hotwolf/LoRaMeshNodes/SSNvD/stls/SSNvD_battery_frame_part1.stl

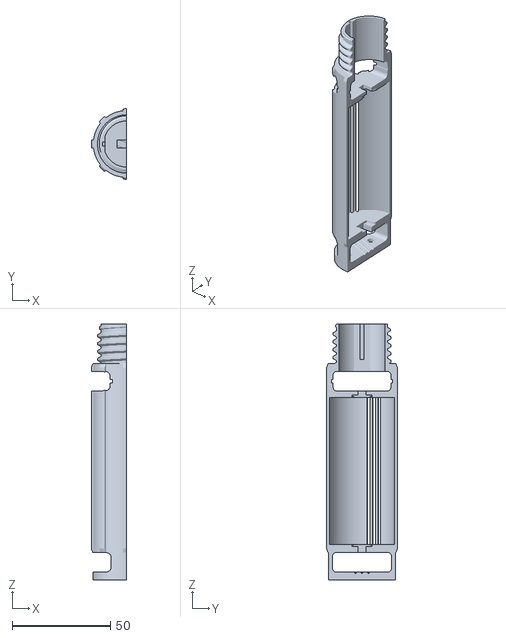
[picture p163: CAD file, 2026-01-20]
SSNvD/stls/SSNvD_battery_frame_part1.stl
18.0 x 36.0 x 130.0
