hotwolf/LoRaMeshNodes/MNvA/stls/MNvA_buttons.stl

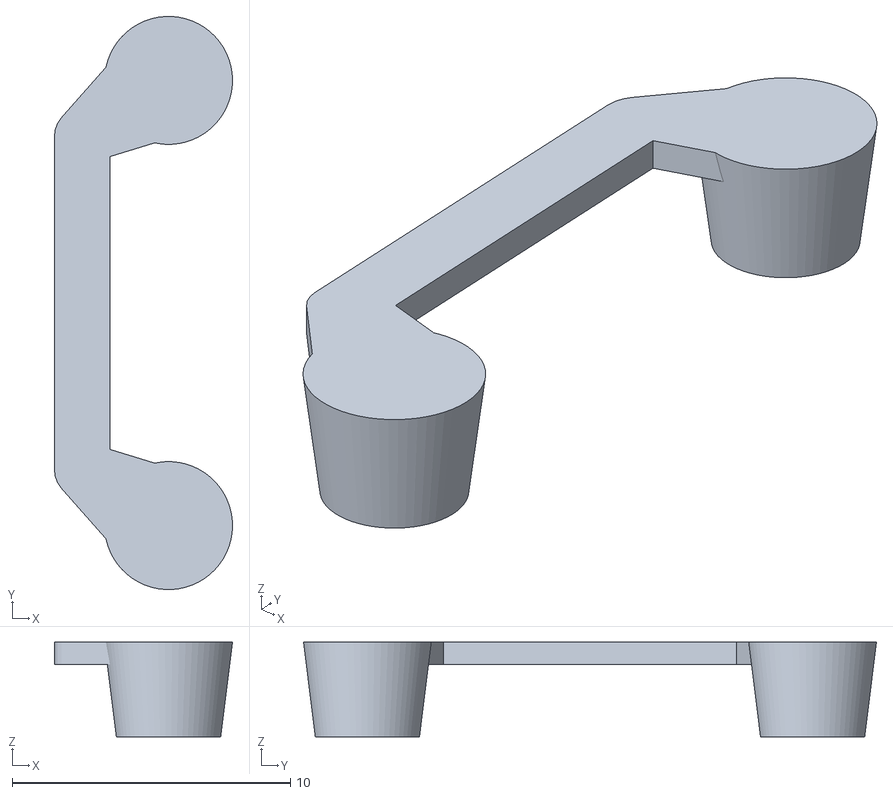
[picture p164: CAD file, 2026-01-26]
MNvA/stls/MNvA_buttons.stl
6.40 x 20.6 x 3.40
