hotwolf/LoRaMeshNodes/MSNvA/stls/MSNvA_stand.stl

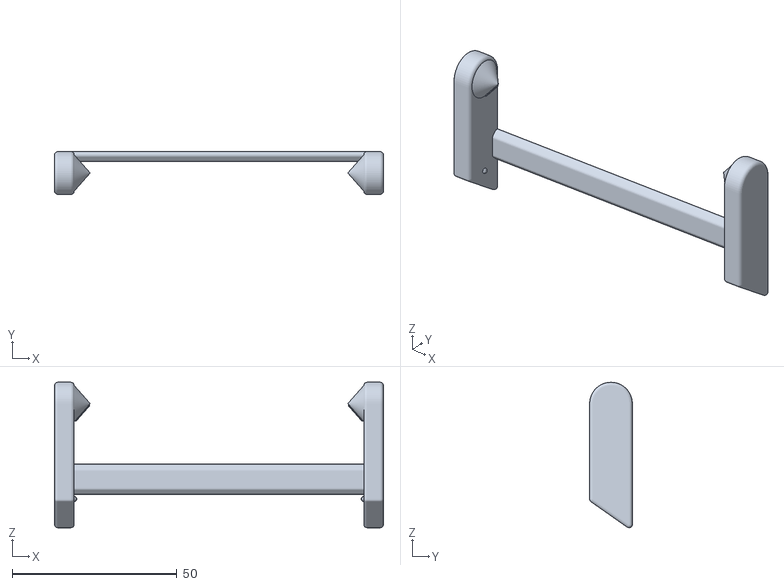
[picture p165: CAD file, 2025-09-03]
MSNvA/stls/MSNvA_stand.stl
100.0 x 13.0 x 44.2
