hotwolf/LoRaMeshNodes/MSNvB/stls/MSNvB_cov.stl

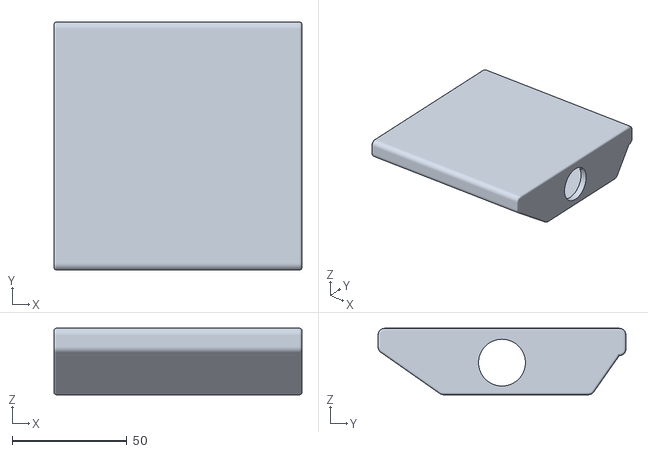
[picture p166: CAD file, 2025-09-03]
MSNvB/stls/MSNvB_cov.stl
108.0 x 108.0 x 29.0
