hotwolf/LoRaMeshNodes/SSNvA/stls/SSNvA_solar_mount.stl

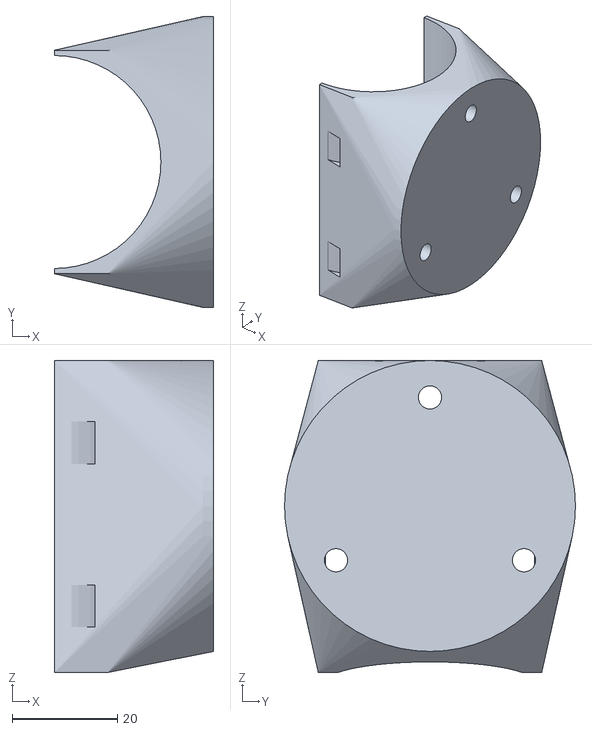
[picture p167: CAD file, 2026-01-20]
SSNvA/stls/SSNvA_solar_mount.stl
30.2 x 55.2 x 59.2
