hotwolf/LoRaMeshNodes/SSNvD/stls/SSNvD_solar_mount.stl

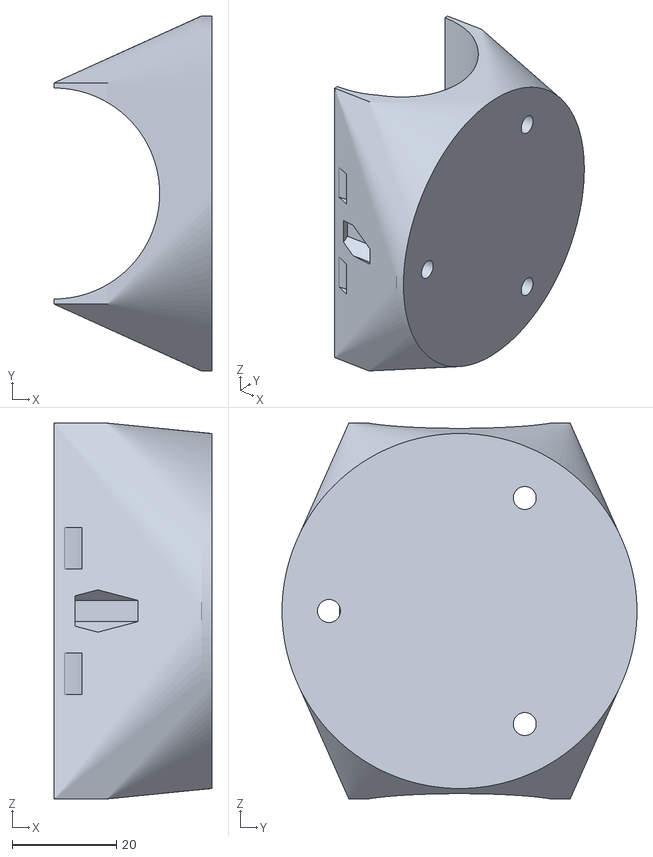
[picture p168: CAD file, 2026-01-20]
SSNvD/stls/SSNvD_solar_mount.stl
30.2 x 68.0 x 72.0
