hotwolf/LoRaMeshNodes/MSNvA/stls/MSNvA_cov.stl

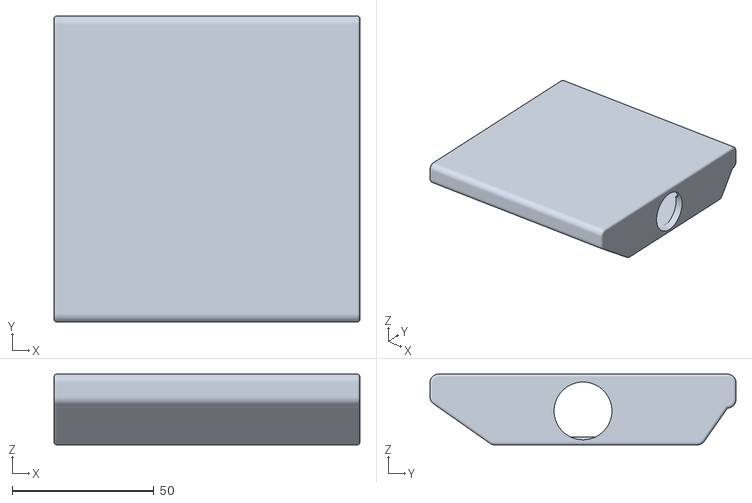
[picture p169: CAD file, 2025-08-17]
MSNvA/stls/MSNvA_cov.stl
108.0 x 108.0 x 25.0
