hotwolf/LoRaMeshNodes/MSNvB/stls/MSNvB_stand.stl

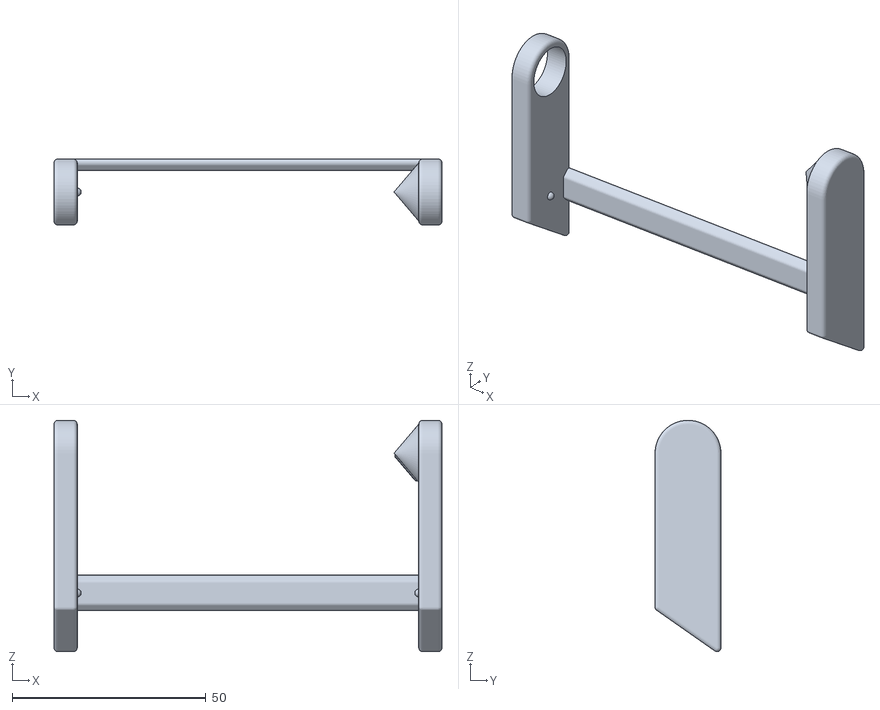
[picture p170: CAD file, 2025-09-03]
MSNvB/stls/MSNvB_stand.stl
100.0 x 17.0 x 59.6
