hotwolf/LoRaMeshNodes/SSNvA/stls/SSNvA_battery_cable_clamp.stl

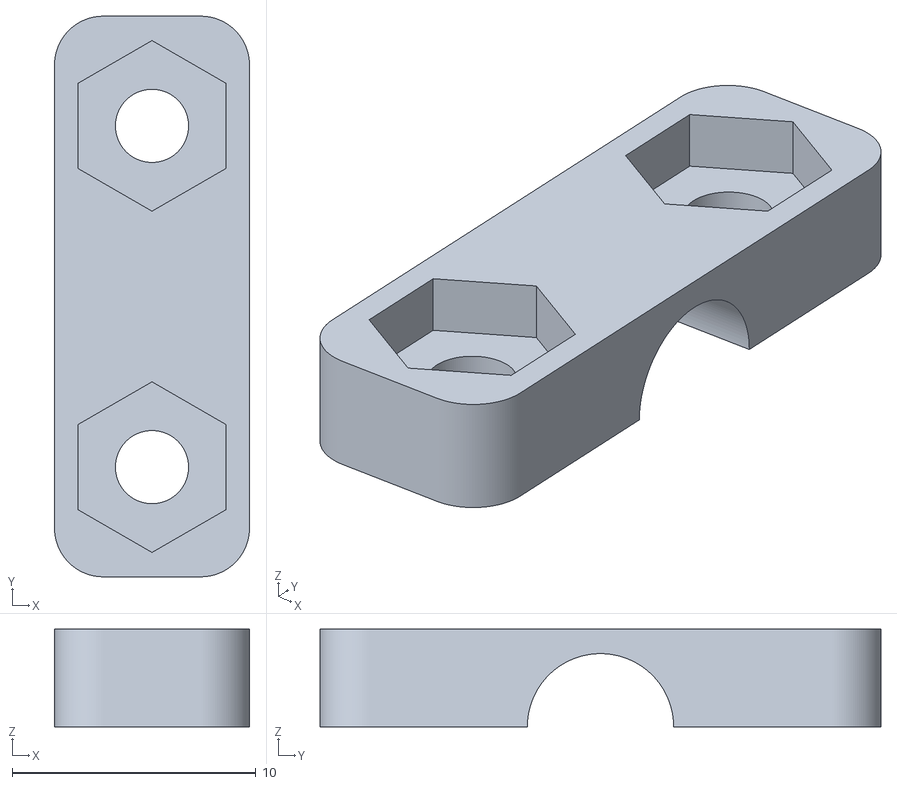
[picture p171: CAD file, 2025-10-28]
SSNvA/stls/SSNvA_battery_cable_clamp.stl
8.00 x 23.0 x 4.00
