hotwolf/LoRaMeshNodes/SSNvB/stls/SSNvB_LOEncMount.stl

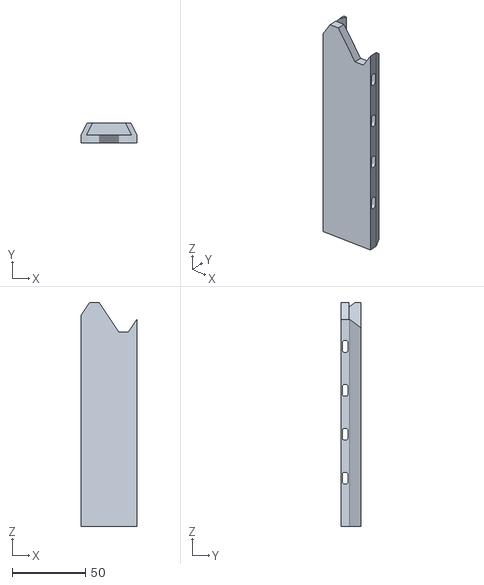
[picture p172: CAD file, 2026-02-28]
SSNvB/stls/SSNvB_LOEncMount.stl
38.0 x 14.0 x 153.0
