hotwolf/LoRaMeshNodes/SSNvD/stls/SSNvD_antenna_top.stl

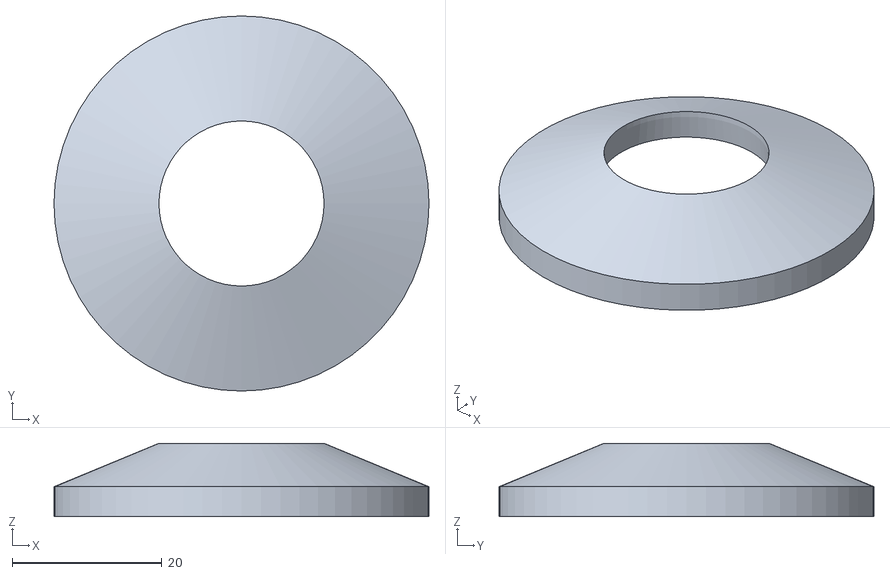
[picture p173: CAD file, 2026-01-19]
SSNvD/stls/SSNvD_antenna_top.stl
50.0 x 50.0 x 9.79
