hotwolf/LoRaMeshNodes/MSNvA/stls/MSNvA_buttons.stl

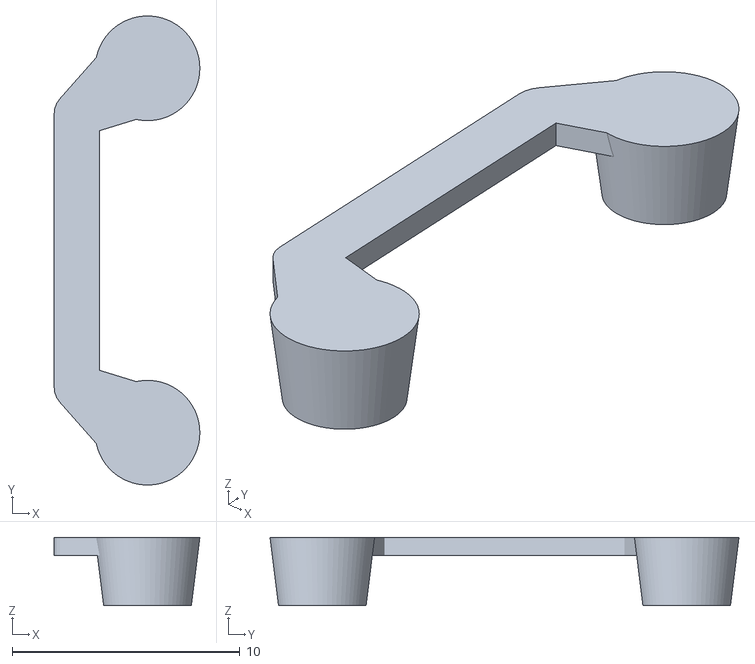
[picture p174: CAD file, 2025-08-17]
MSNvA/stls/MSNvA_buttons.stl
6.40 x 20.6 x 3.00
