hotwolf/LoRaMeshNodes/SSNvB/stls/SSNvB_lEndcap.stl

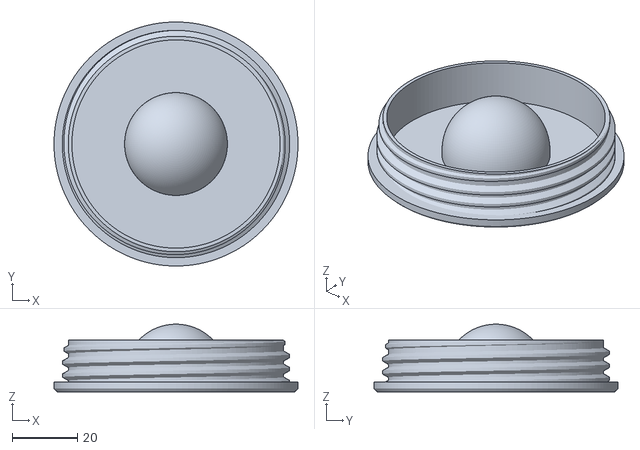
[picture p175: CAD file, 2026-02-17]
SSNvB/stls/SSNvB_lEndcap.stl
75.0 x 75.0 x 20.8
