hotwolf/LoRaMeshNodes/SSNvD/stls/SSNvD_end_cap_ring.stl

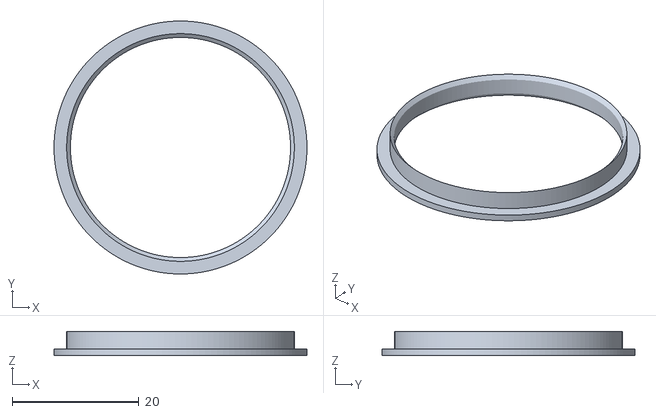
[picture p176: CAD file, 2026-01-19]
SSNvD/stls/SSNvD_end_cap_ring.stl
40.0 x 40.0 x 3.80
