hotwolf/LoRaMeshNodes/SSNvA/stls/SSNvA_antenna_part2.stl

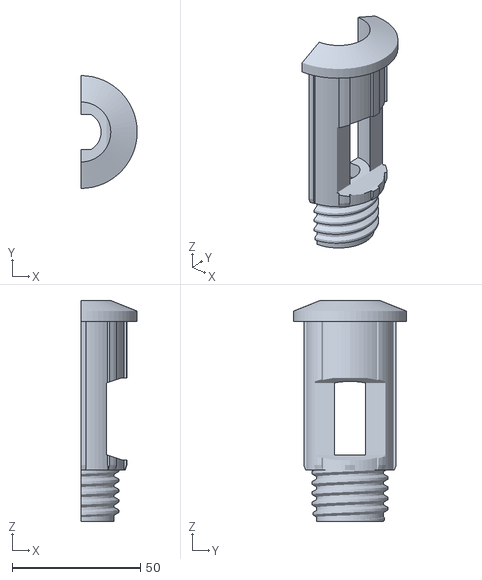
[picture p177: CAD file, 2025-10-27]
SSNvA/stls/SSNvA_antenna_part2.stl
22.0 x 44.0 x 86.1
