hotwolf/LoRaMeshNodes/SSNvB/stls/SSNvB_antennaMountFastener.stl

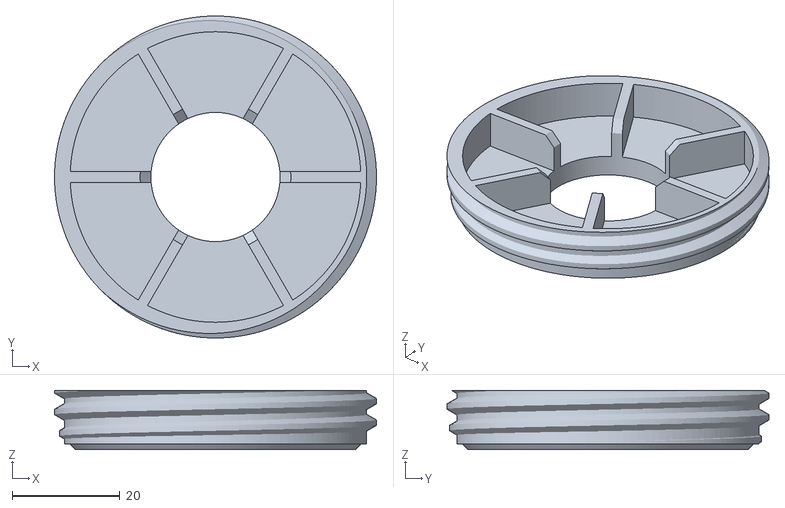
[picture p178: CAD file, 2026-02-17]
SSNvB/stls/SSNvB_antennaMountFastener.stl
59.8 x 59.8 x 11.0
