hotwolf/LoRaMeshNodes/SSNvD/stls/SSNvD_battery_cable_clamp.stl

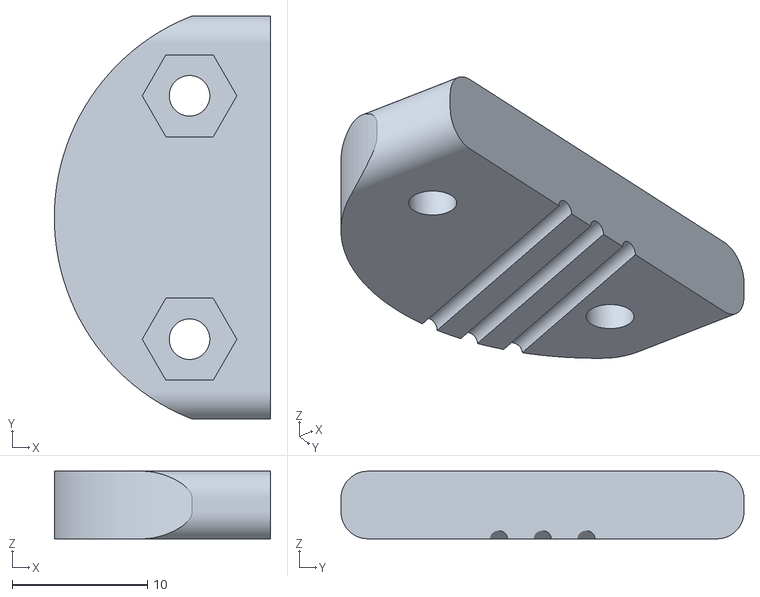
[picture p179: CAD file, 2026-01-19]
SSNvD/stls/SSNvD_battery_cable_clamp.stl
16.0 x 29.8 x 5.00
