hotwolf/LoRaMeshNodes/SSNvB/stls/SSNvB_uEndcap.stl

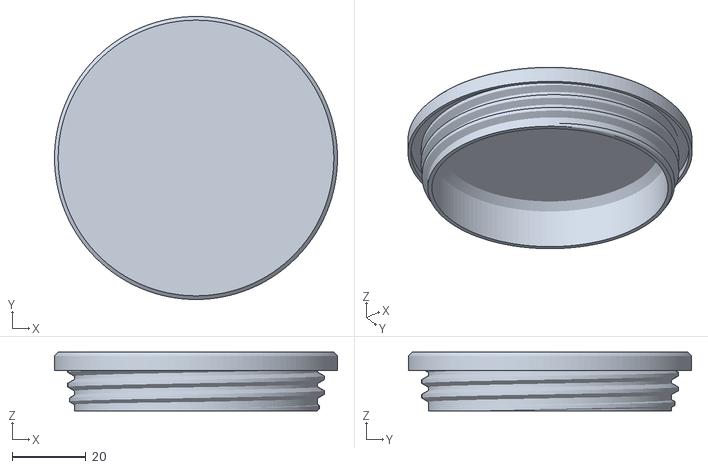
[picture p180: CAD file, 2026-02-17]
SSNvB/stls/SSNvB_uEndcap.stl
77.0 x 77.0 x 16.0
