hotwolf/LoRaMeshNodes/SSNvD/stls/SSNvD_radio_frame_part2.stl

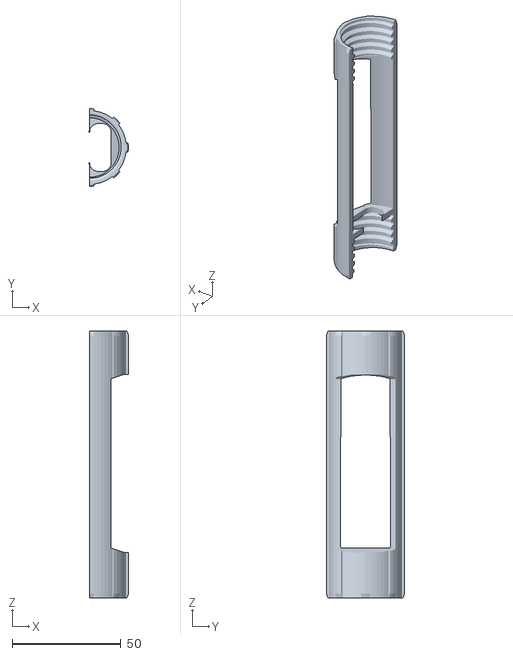
[picture p181: CAD file, 2026-01-19]
SSNvD/stls/SSNvD_radio_frame_part2.stl
18.0 x 36.0 x 123.0
