hotwolf/LoRaMeshNodes/SSNvB/stls/SSNvB_battery_frame_part1.stl

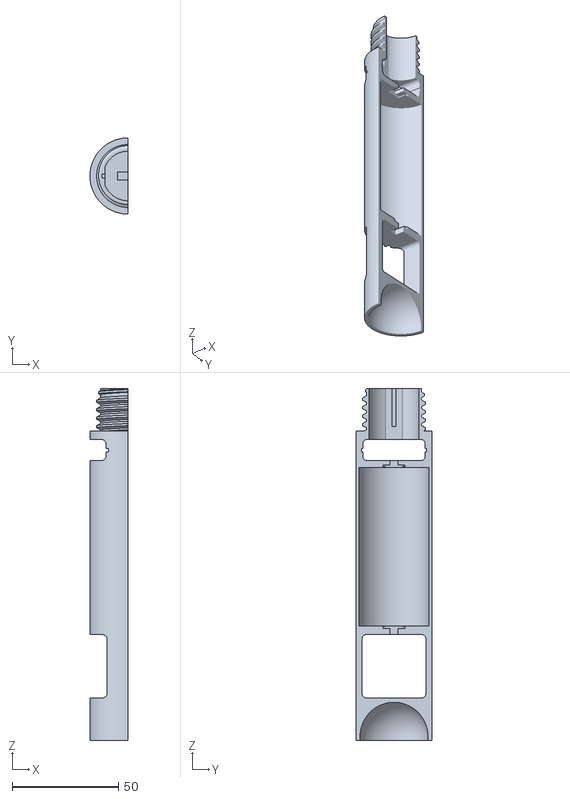
[picture p183: CAD file, 2026-02-15]
SSNvB/stls/SSNvB_battery_frame_part1.stl
18.0 x 36.0 x 166.0
