hotwolf/LoRaMeshNodes/SSNvD/stls/SSNvD_spacer.stl

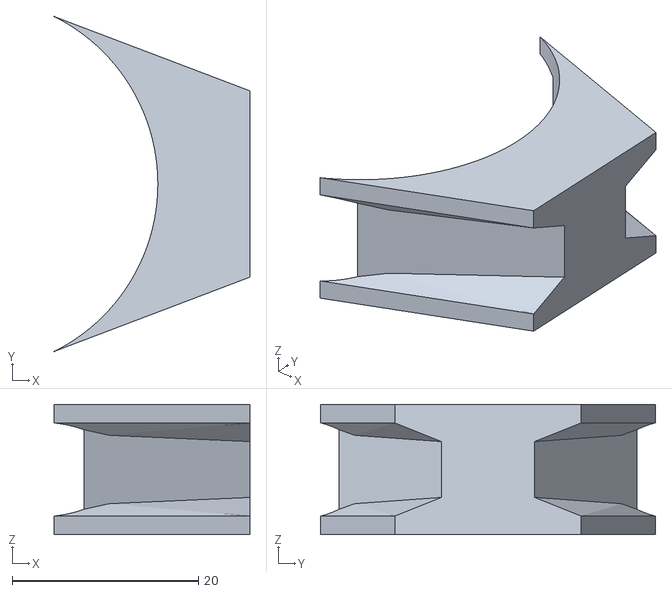
[picture p184: CAD file, 2026-01-19]
SSNvD/stls/SSNvD_spacer.stl
21.1 x 36.0 x 14.0
