hotwolf/LoRaMeshNodes/SSNvA/stls/SSNvA_battery_frame_part2.stl

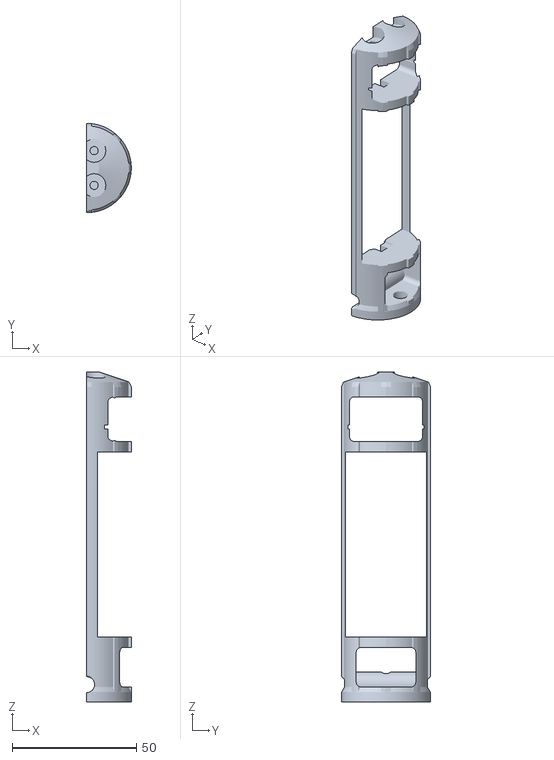
[picture p185: CAD file, 2025-10-27]
SSNvA/stls/SSNvA_battery_frame_part2.stl
18.0 x 36.0 x 133.0
