hotwolf/LoRaMeshNodes/SSNvB/stls/SSNvB_battery_frame_part2.stl

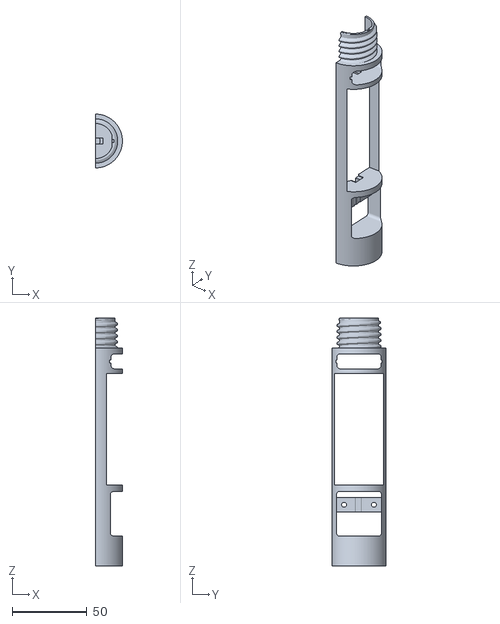
[picture p186: CAD file, 2026-02-15]
SSNvB/stls/SSNvB_battery_frame_part2.stl
18.0 x 36.0 x 166.0
