hotwolf/LoRaMeshNodes/SSNvD/stls/SSNvD_end_cap.stl

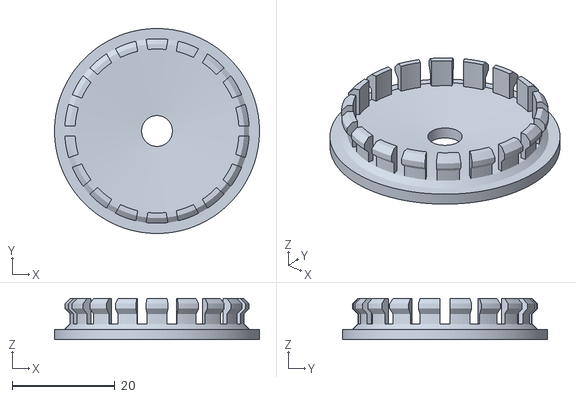
[picture p187: CAD file, 2026-01-19]
SSNvD/stls/SSNvD_end_cap.stl
40.0 x 40.0 x 8.00
