hotwolf/LoRaMeshNodes/SSNvA/stls/SSNvA_antenna_top.stl

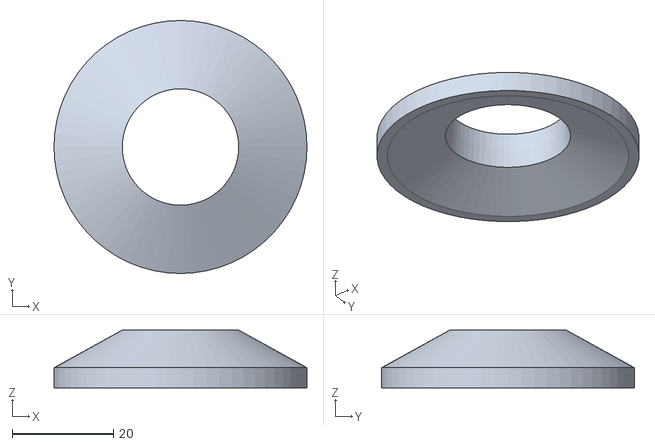
[picture p188: CAD file, 2025-10-20]
SSNvA/stls/SSNvA_antenna_top.stl
50.0 x 50.0 x 11.4
