hotwolf/LoRaMeshNodes/SSNvB/stls/SSNvB_EndcapThread.stl

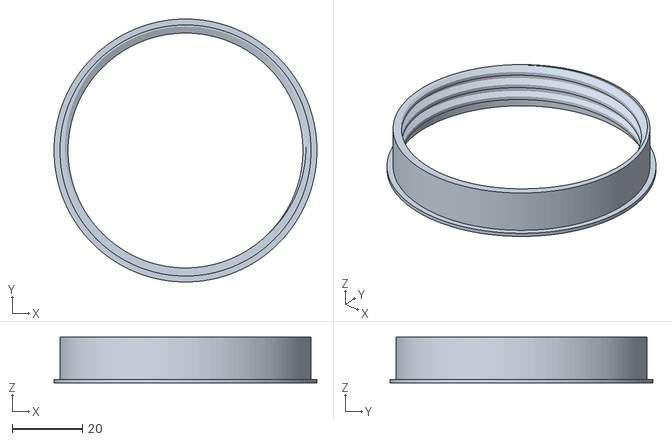
[picture p189: CAD file, 2026-02-15]
SSNvB/stls/SSNvB_EndcapThread.stl
75.0 x 75.0 x 13.0
