hotwolf/LoRaMeshNodes/SSNvD/stls/SSNvD_radio_frame_part1.stl

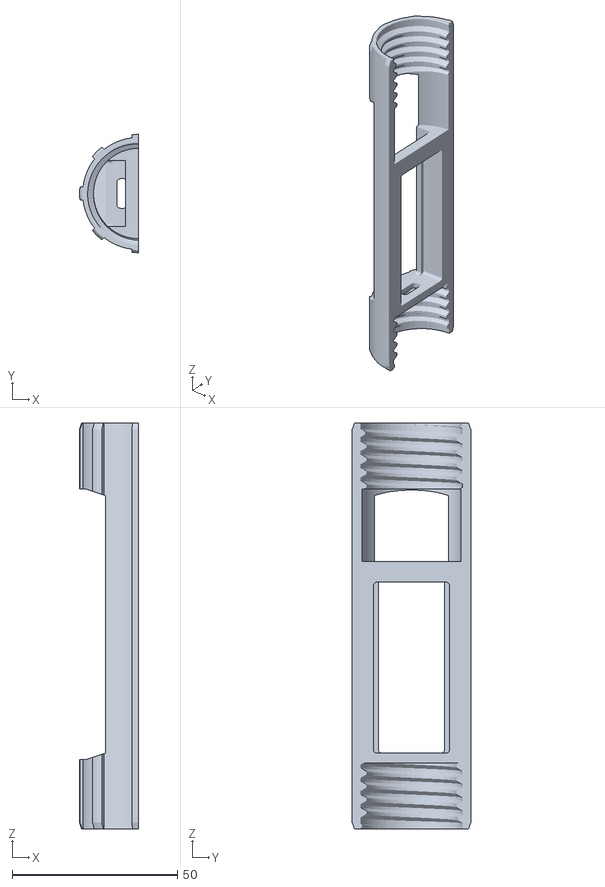
[picture p190: CAD file, 2026-01-19]
SSNvD/stls/SSNvD_radio_frame_part1.stl
18.0 x 36.0 x 123.0
