hotwolf/LoRaMeshNodes/SSNvA/stls/SSNvA_scrutonM40.stl

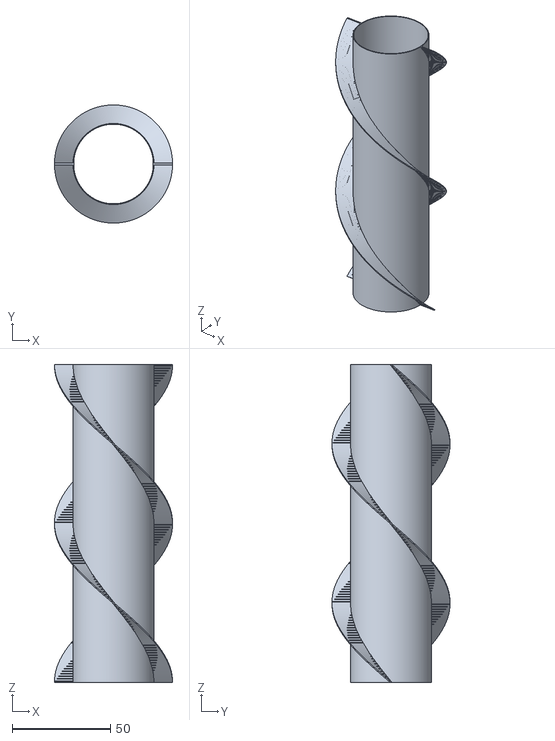
[picture p191: CAD file, 2025-10-20]
SSNvA/stls/SSNvA_scrutonM40.stl
60.0 x 60.0 x 161.6
