hotwolf/LoRaMeshNodes/SSNvB/stls/SSNvB_antenna.stl

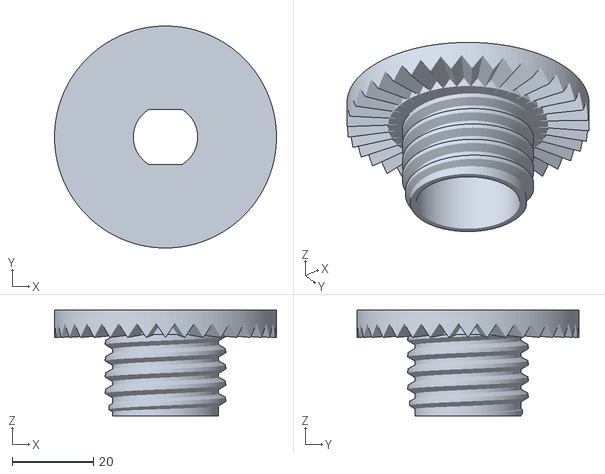
[picture p192: CAD file, 2026-02-15]
SSNvB/stls/SSNvB_antenna.stl
54.6 x 54.6 x 26.0
