hotwolf/LoRaMeshNodes/SSNvD/stls/SSNvD_antenna_part1.stl

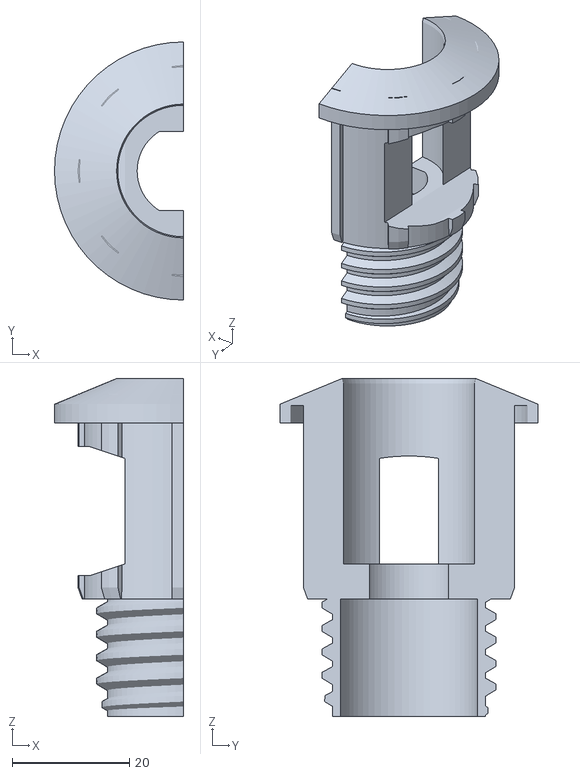
[picture p193: CAD file, 2026-01-19]
SSNvD/stls/SSNvD_antenna_part1.stl
22.0 x 44.0 x 57.6
