hotwolf/LoRaMeshNodes/SSNvA/stls/SSNvA_cable_clamp.stl

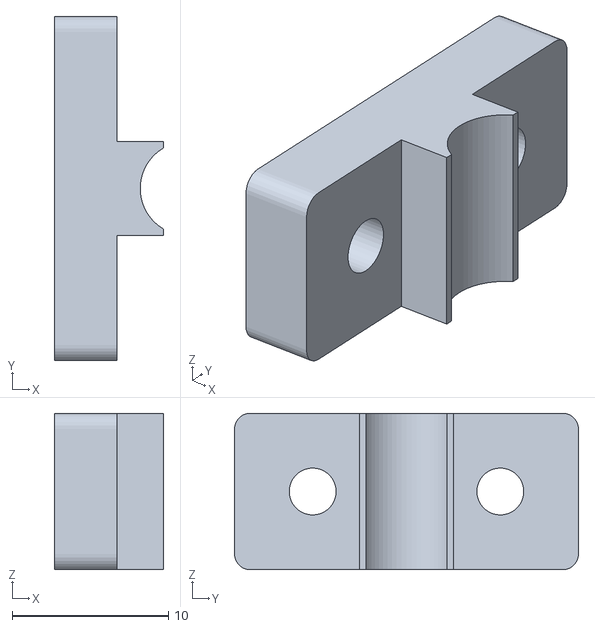
[picture p194: CAD file, 2025-10-20]
SSNvA/stls/SSNvA_cable_clamp.stl
7.00 x 22.0 x 10.0
