hotwolf/LoRaMeshNodes/SSNvB/stls/SSNvB_antennaMountThread.stl

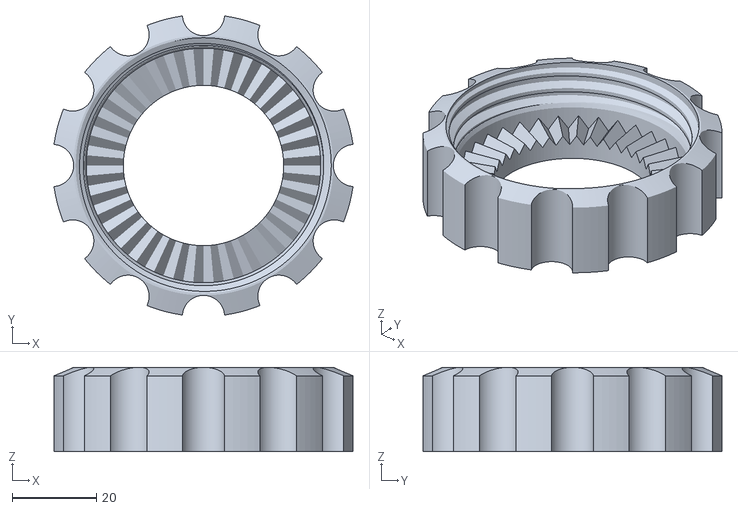
[picture p195: CAD file, 2026-02-15]
SSNvB/stls/SSNvB_antennaMountThread.stl
70.9 x 70.9 x 20.0
