hotwolf/LoRaMeshNodes/SSNvB/stls/SSNvB_battery_cable_clamp.stl

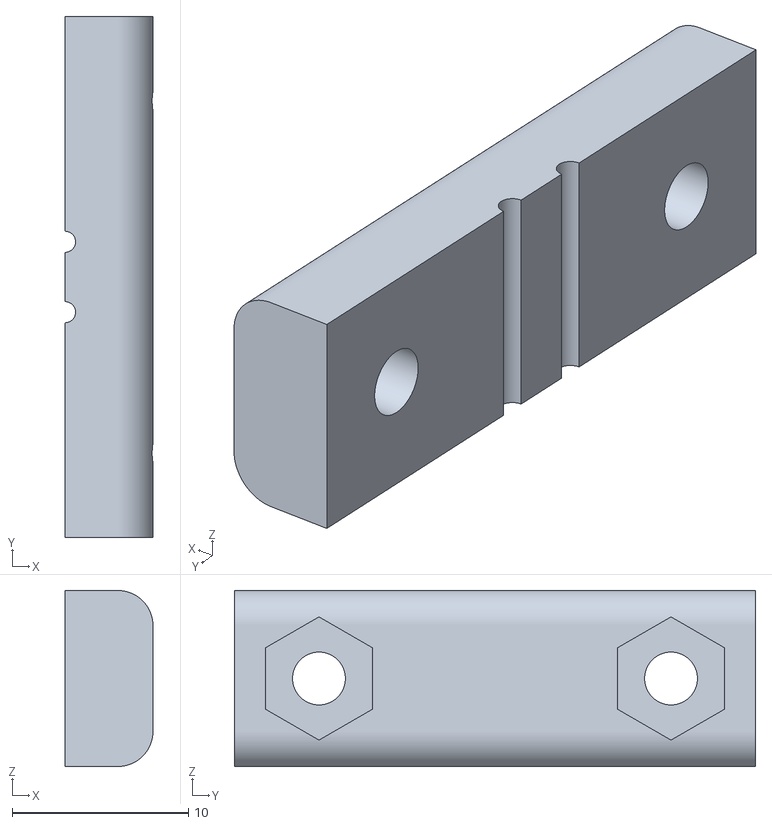
[picture p196: CAD file, 2026-02-15]
SSNvB/stls/SSNvB_battery_cable_clamp.stl
5.00 x 29.6 x 10.0
