hotwolf/LoRaMeshNodes/SSNvA/bom/SSNvA_pole_assembly.txt

SSNvA_pole_assembly:
Vitamins:
  1 Conduit diameter 40mmlength 2000mm

Printed:
  2 SSNvA_scrutonM40.stl
