hotwolf/LoRaMeshNodes/SSNvA/bom/SSNvA_radio_frame_assembly.txt

SSNvA_radio_frame_assembly:
Printed:
  1 SSNvA_radio_frame_part1.stl
  1 SSNvA_radio_frame_part2.stl
