hotwolf/LoRaMeshNodes/SSNvA/bom/SSNvA_top_assembly.txt

SSNvA_top_assembly:

Assemblies:
  1 SSNvA_antenna_assembly
  1 SSNvA_radio_assembly
