hotwolf/LoRaMeshNodes/MSNvB/bom/MSNvB_assembly.txt

MSNvB_assembly:
Printed:
  1 MSNvB_cov.stl

Assemblies:
  1 MSNvB_enc_assembly
