hotwolf/LoRaMeshNodes/MSNvA/bom/MSNvA_enc_assembly.txt

MSNvA_enc_assembly:
Vitamins:
  1 Solar Panel 100x100mm² 5V 3W

Printed:
  1 MSNvA_top.stl

Assemblies:
  1 MSNvA_lEnc_assembly
