hotwolf/LoRaMeshNodes/MSNvA/bom/MSNvA_assembly.txt

MSNvA_assembly:
Printed:
  1 MSNvA_cov.stl

Assemblies:
  1 MSNvA_enc_assembly
