hotwolf/LoRaMeshNodes/MSNvA/bom/MSNvA_lEnc_assembly.txt

MSNvA_lEnc_assembly:
Vitamins:
  1 Lithium-Polymer-Akku 3,7V 2500mAh
  1 Solar Panel 100x100mm² 5V 3W
  1 Antenna 20cm LoRa Antenna
  1 Nut M6.25 x 1.8mm 
  1 Heltec T144
  1 Heltec L76K_GNSS Module
  1 Washer star M6.4 x 0.6mm

Printed:
  1 MSNvA_buttons.stl
  1 MSNvA_lEnc.stl
  1 MSNvA_stand.stl
