hotwolf/LoRaMeshNodes/LiFePo4Charger/assemblies/LiFePo4Charger_assembly.png

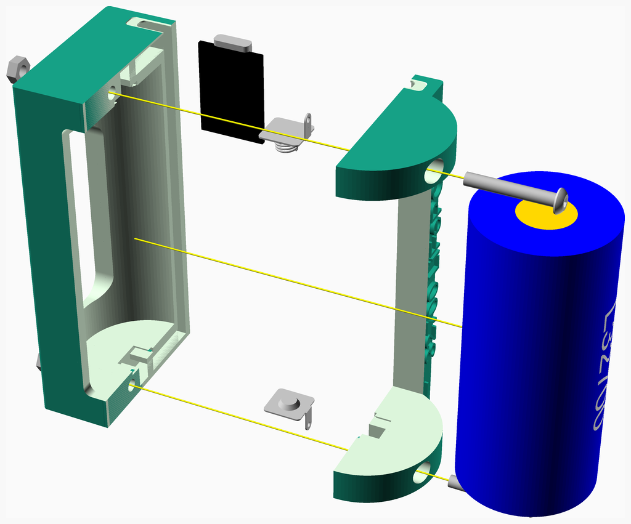
LiFePo4Charger/assemblies/LiFePo4Charger_assembly.png
