hotwolf/LoRaMeshNodes/MNvA/assemblies/MNvA_assembled_tn.png

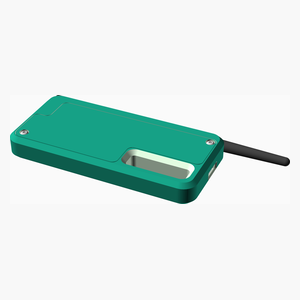
MNvA/assemblies/MNvA_assembled_tn.png
