hotwolf/LoRaMeshNodes/MNvA/assemblies/MNvA_assembly_tn.png

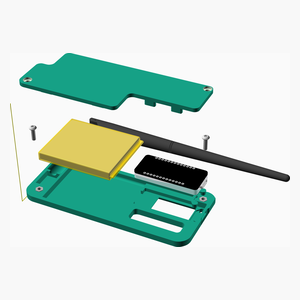
MNvA/assemblies/MNvA_assembly_tn.png
