hotwolf/LoRaMeshNodes/MNvA/assemblies/MNvA_lEnc_assembly_tn.png

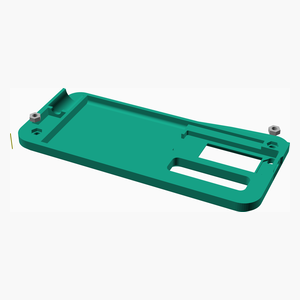
MNvA/assemblies/MNvA_lEnc_assembly_tn.png
