hotwolf/LoRaMeshNodes/MNvB/assemblies/MNvB_assembly.png

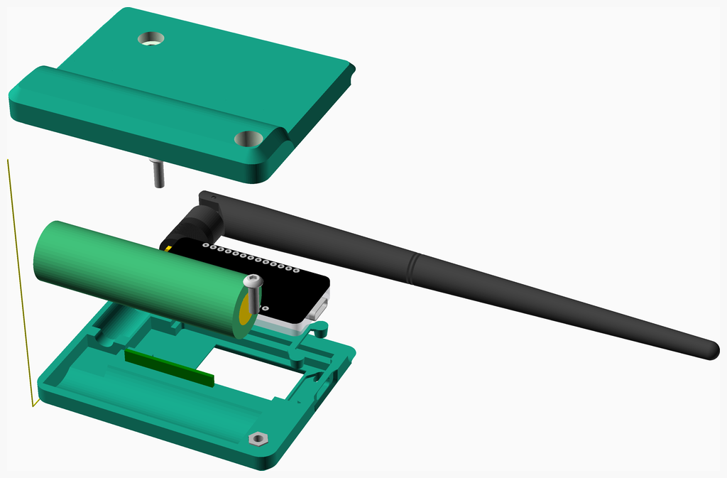
MNvB/assemblies/MNvB_assembly.png
