hotwolf/LoRaMeshNodes/MNvB/assemblies/MNvB_lEnc_assembled.png

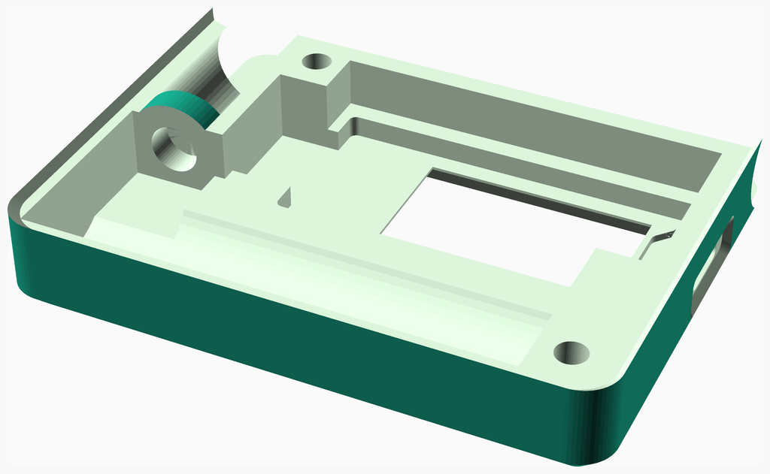
MNvB/assemblies/MNvB_lEnc_assembled.png
