hotwolf/LoRaMeshNodes/MNvB/assemblies/MNvB_lEnc_assembly.png

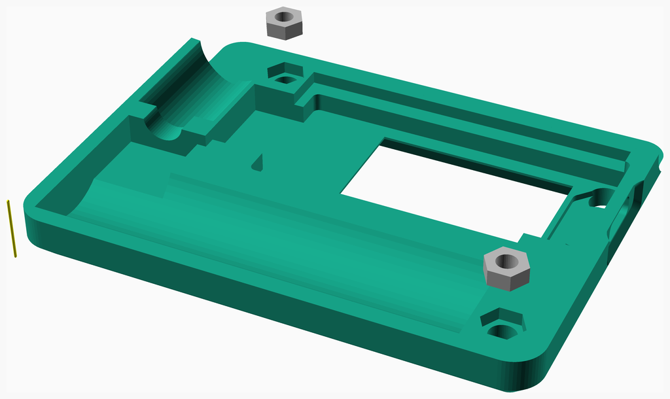
MNvB/assemblies/MNvB_lEnc_assembly.png
