hotwolf/LoRaMeshNodes/MSNvA/assemblies/MSNvA_assembled_tn.png

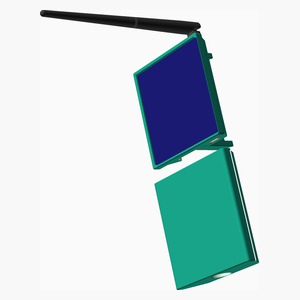
MSNvA/assemblies/MSNvA_assembled_tn.png
