hotwolf/LoRaMeshNodes/MSNvA/assemblies/MSNvA_assembly_tn.png

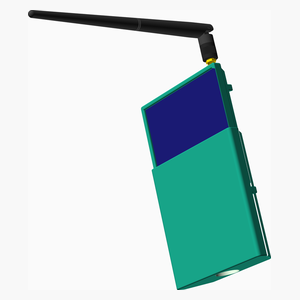
MSNvA/assemblies/MSNvA_assembly_tn.png
