hotwolf/LoRaMeshNodes/MSNvA/assemblies/MSNvA_enc_assembly_tn.png

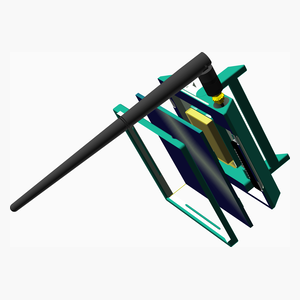
MSNvA/assemblies/MSNvA_enc_assembly_tn.png
