hotwolf/LoRaMeshNodes/MSNvA/assemblies/MSNvA_lEnc_assembly_tn.png

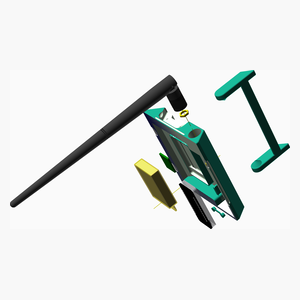
MSNvA/assemblies/MSNvA_lEnc_assembly_tn.png
