hotwolf/LoRaMeshNodes/MSNvB/assemblies/MSNvB_assembly_tn.png

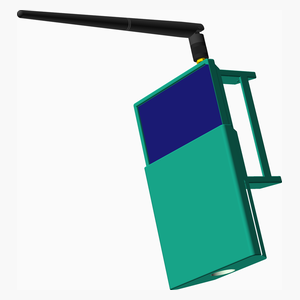
MSNvB/assemblies/MSNvB_assembly_tn.png
