hotwolf/LoRaMeshNodes/MSNvB/assemblies/MSNvB_enc_assembly_tn.png

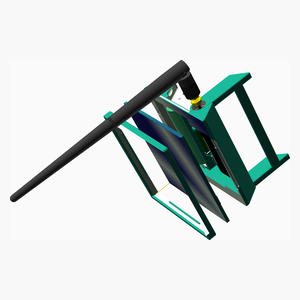
MSNvB/assemblies/MSNvB_enc_assembly_tn.png
