hotwolf/LoRaMeshNodes/MSNvB/assemblies/MSNvB_lEnc_assembly_tn.png

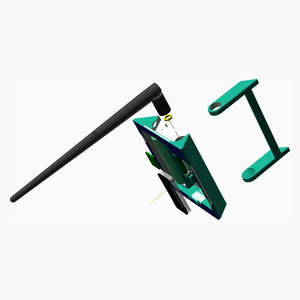
MSNvB/assemblies/MSNvB_lEnc_assembly_tn.png
