hotwolf/LoRaMeshNodes/SSNvA/assemblies/SSNvA_antenna_assembly.png

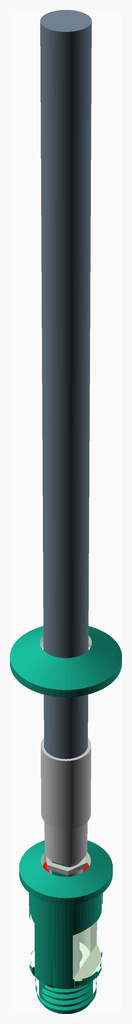
SSNvA/assemblies/SSNvA_antenna_assembly.png
