hotwolf/LoRaMeshNodes/SSNvA/assemblies/SSNvA_antenna_frame_assembled.png

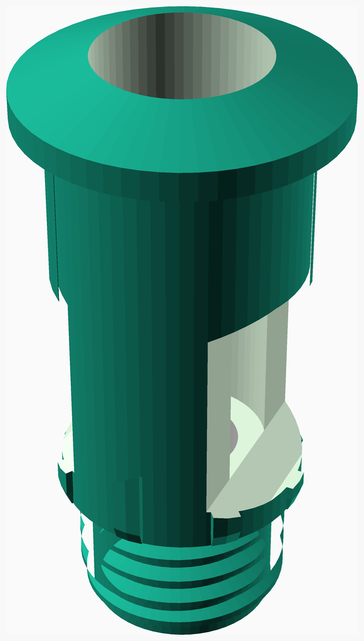
SSNvA/assemblies/SSNvA_antenna_frame_assembled.png
