hotwolf/LoRaMeshNodes/SSNvA/assemblies/SSNvA_antenna_frame_assembly.png

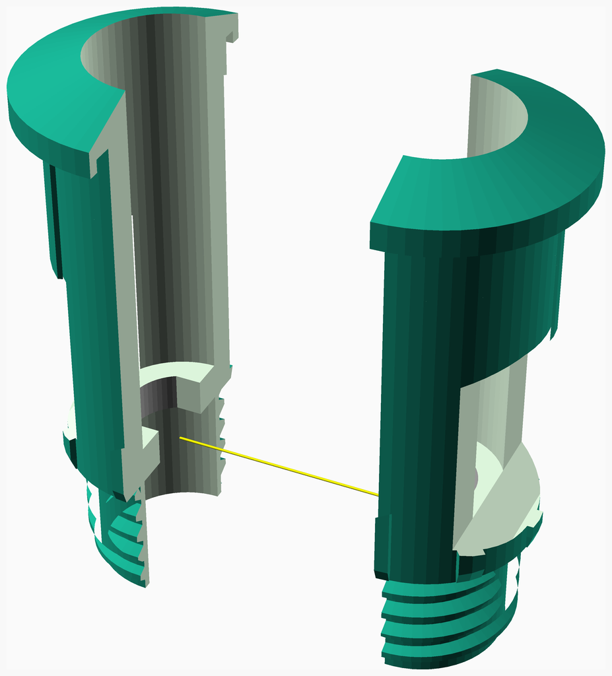
SSNvA/assemblies/SSNvA_antenna_frame_assembly.png
