hotwolf/LoRaMeshNodes/SSNvA/assemblies/SSNvA_assembly.png

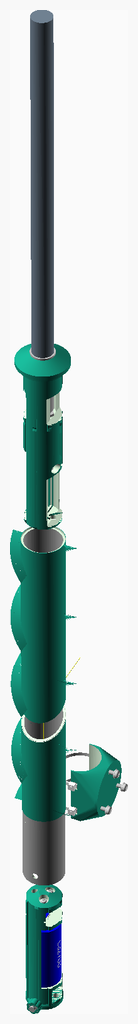
SSNvA/assemblies/SSNvA_assembly.png
