hotwolf/LoRaMeshNodes/SSNvA/assemblies/SSNvA_battery_assembled.png

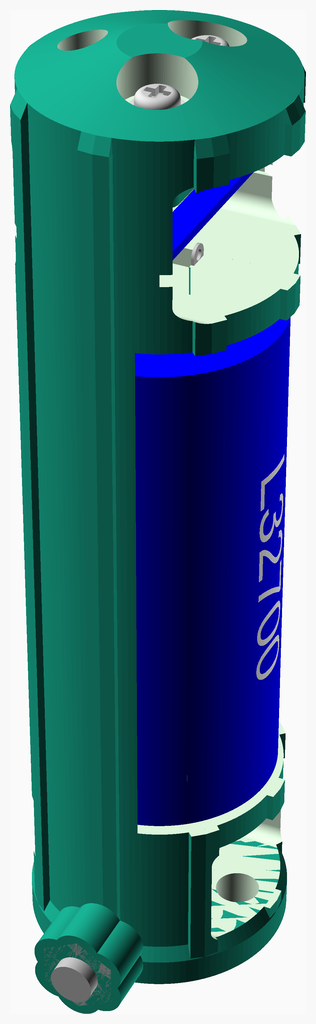
SSNvA/assemblies/SSNvA_battery_assembled.png
