hotwolf/LoRaMeshNodes/SSNvA/assemblies/SSNvA_battery_assembly.png

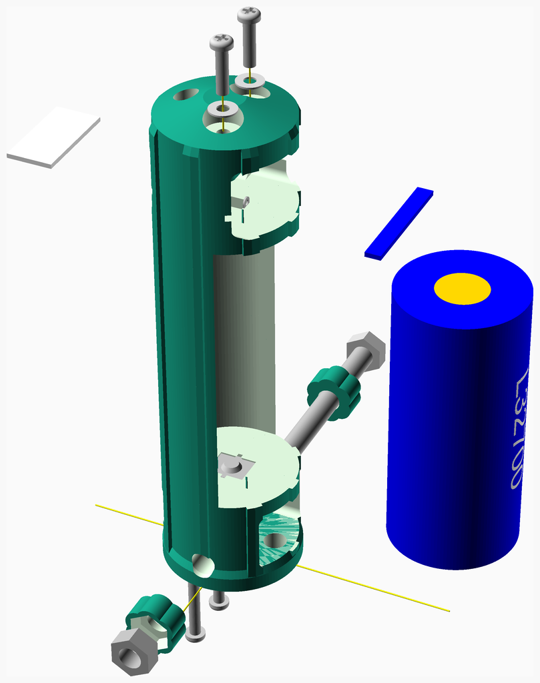
SSNvA/assemblies/SSNvA_battery_assembly.png
