hotwolf/LoRaMeshNodes/SSNvA/assemblies/SSNvA_battery_cable_clamp_assembled.png

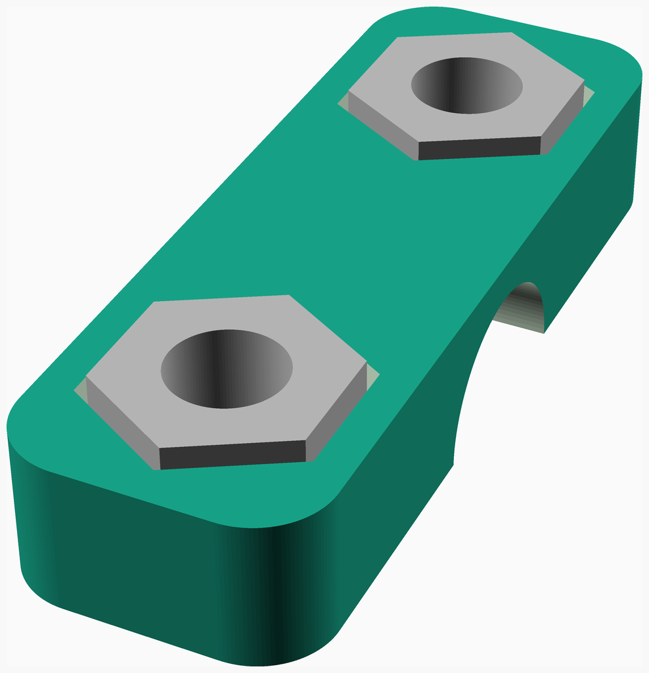
SSNvA/assemblies/SSNvA_battery_cable_clamp_assembled.png
