hotwolf/LoRaMeshNodes/SSNvA/assemblies/SSNvA_battery_frame_assembled.png

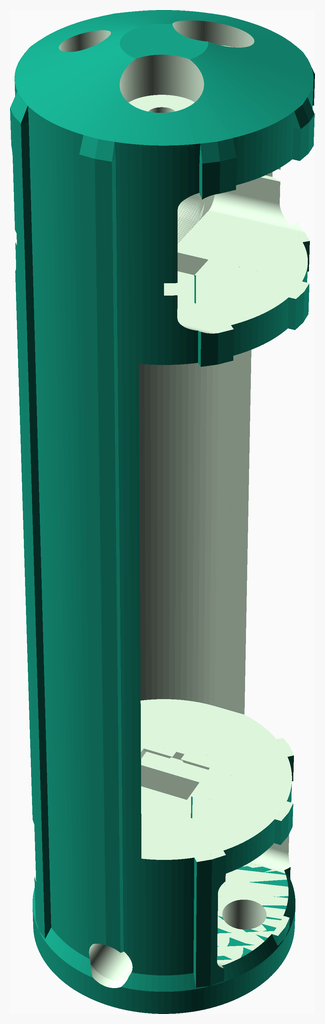
SSNvA/assemblies/SSNvA_battery_frame_assembled.png
