hotwolf/LoRaMeshNodes/SSNvA/assemblies/SSNvA_pole_assembled.png

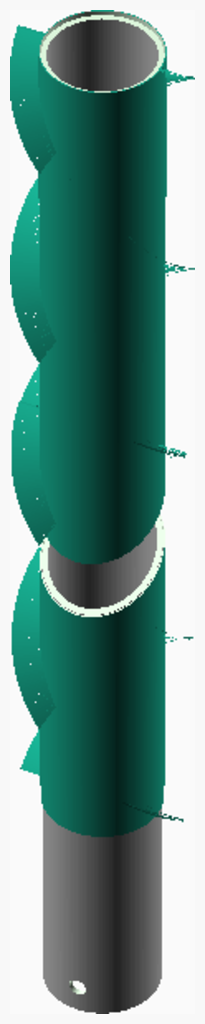
SSNvA/assemblies/SSNvA_pole_assembled.png
