hotwolf/LoRaMeshNodes/SSNvA/assemblies/SSNvA_radio_assembled.png

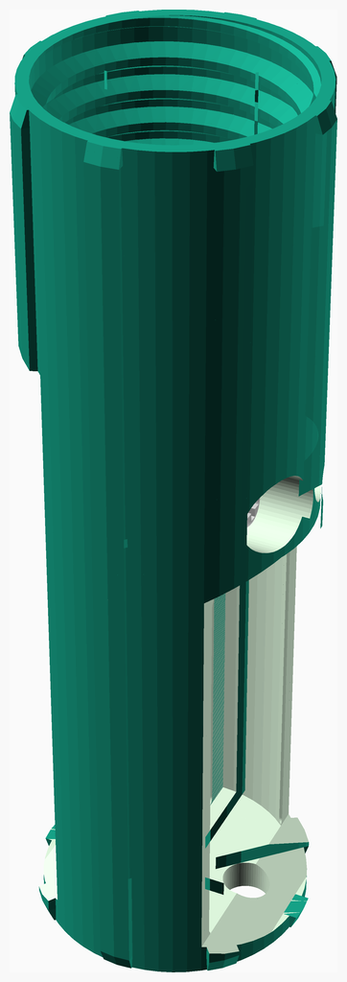
SSNvA/assemblies/SSNvA_radio_assembled.png
