hotwolf/LoRaMeshNodes/SSNvA/assemblies/SSNvA_radio_frame_assembly.png

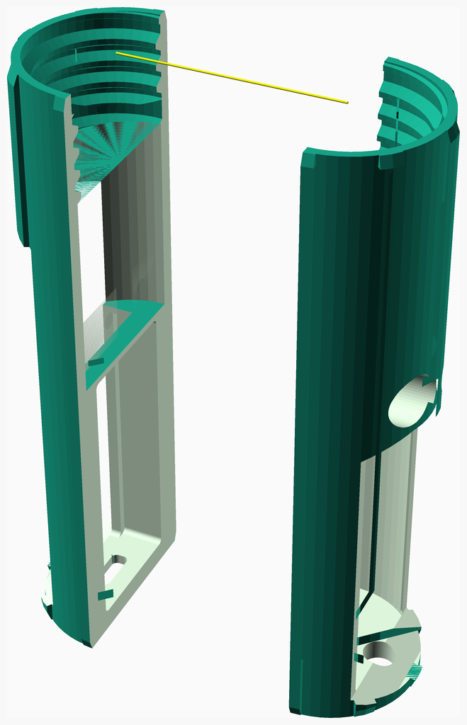
SSNvA/assemblies/SSNvA_radio_frame_assembly.png
