hotwolf/LoRaMeshNodes/SSNvA/assemblies/SSNvA_solar_mount_assembled.png

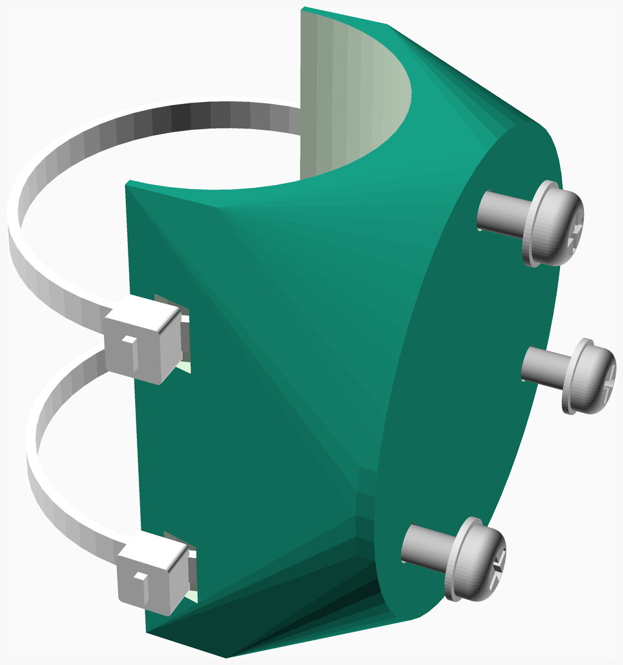
SSNvA/assemblies/SSNvA_solar_mount_assembled.png
