hotwolf/LoRaMeshNodes/SSNvA/assemblies/SSNvA_solar_mount_assembly.png

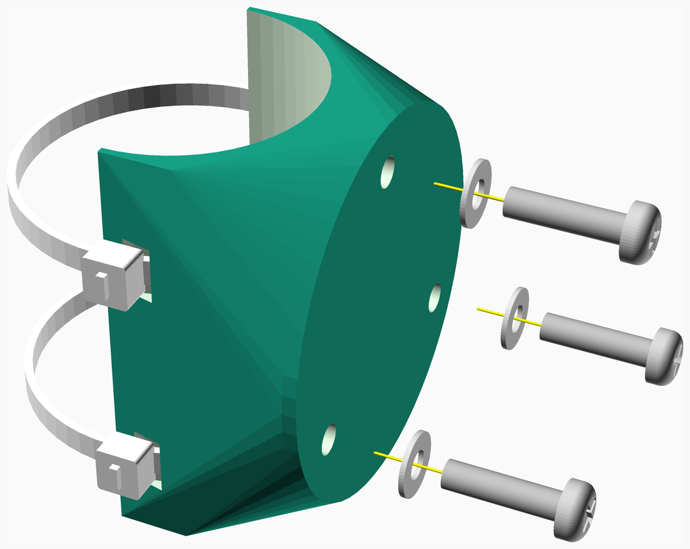
SSNvA/assemblies/SSNvA_solar_mount_assembly.png
