hotwolf/LoRaMeshNodes/SSNvB/assemblies/SSNvB_antenna_assembly.png

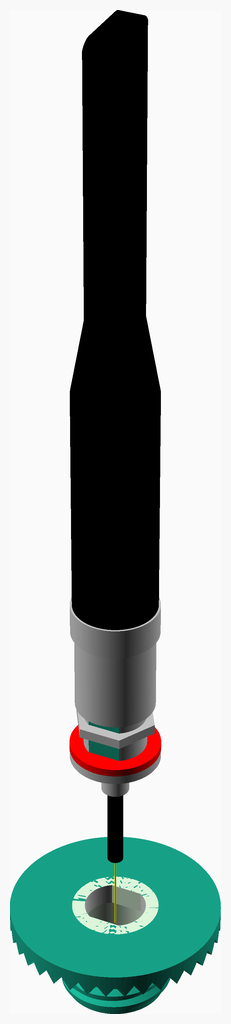
SSNvB/assemblies/SSNvB_antenna_assembly.png
