hotwolf/LoRaMeshNodes/SSNvB/assemblies/SSNvB_battery_assembled.png

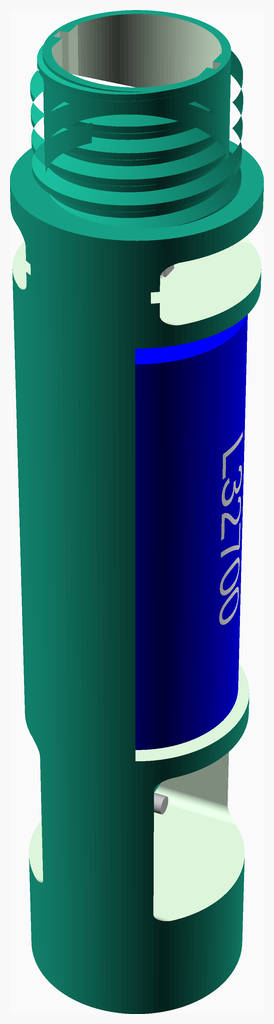
SSNvB/assemblies/SSNvB_battery_assembled.png
