hotwolf/LoRaMeshNodes/SSNvB/assemblies/SSNvB_battery_assembly.png

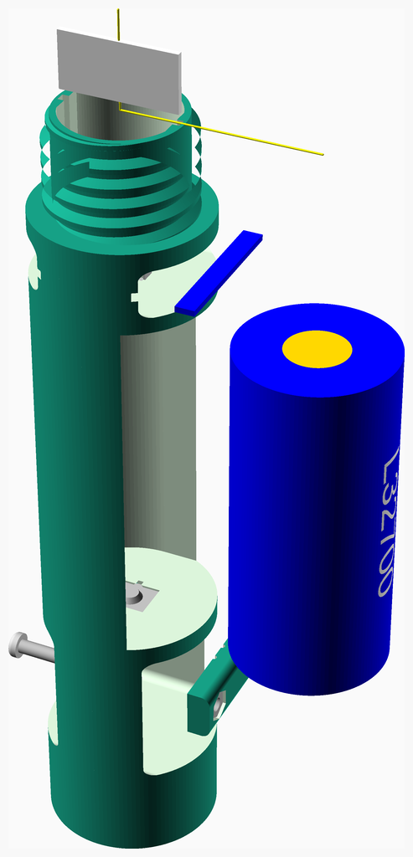
SSNvB/assemblies/SSNvB_battery_assembly.png
