hotwolf/LoRaMeshNodes/SSNvB/assemblies/SSNvB_battery_cable_clamp_assembled.png

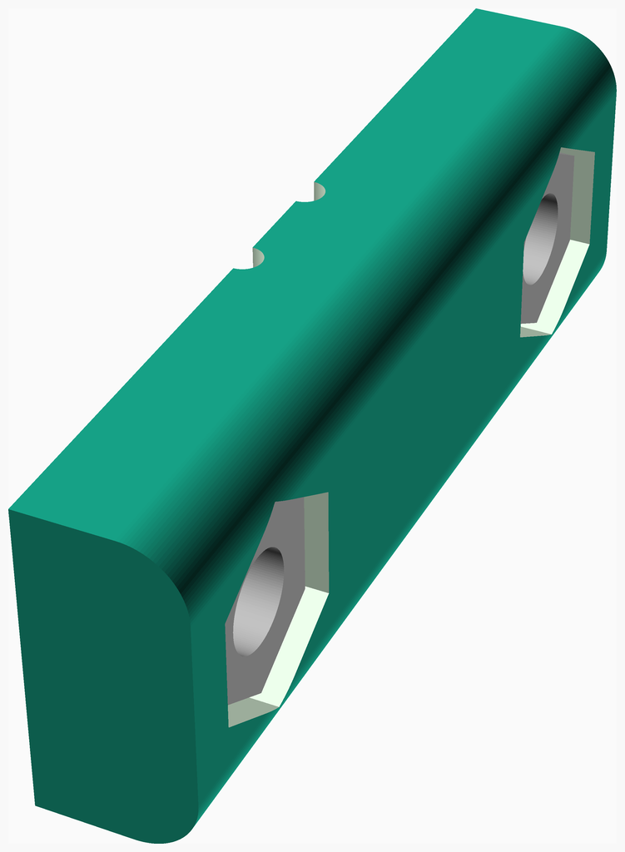
SSNvB/assemblies/SSNvB_battery_cable_clamp_assembled.png
