hotwolf/LoRaMeshNodes/SSNvB/assemblies/SSNvB_battery_cable_clamp_assembly.png

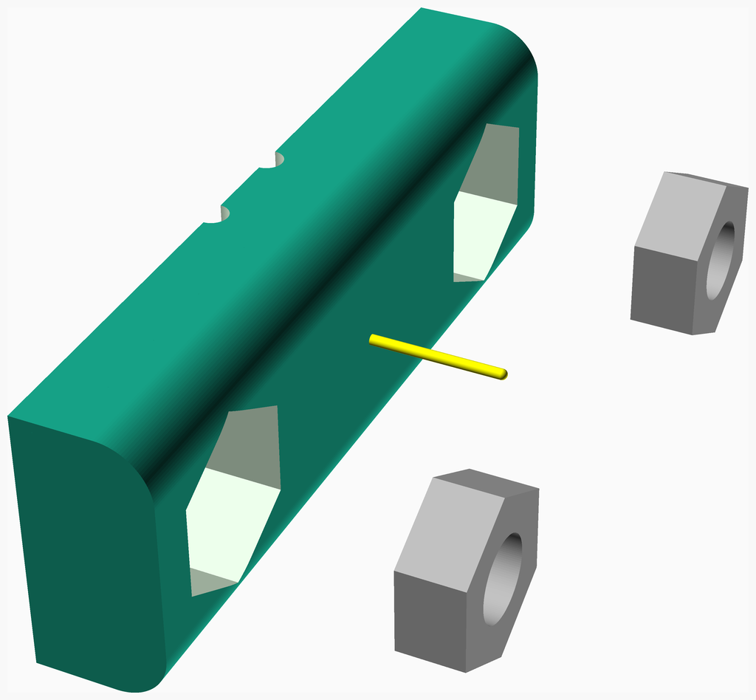
SSNvB/assemblies/SSNvB_battery_cable_clamp_assembly.png
