hotwolf/LoRaMeshNodes/SSNvB/assemblies/SSNvB_battery_frame_assembled.png

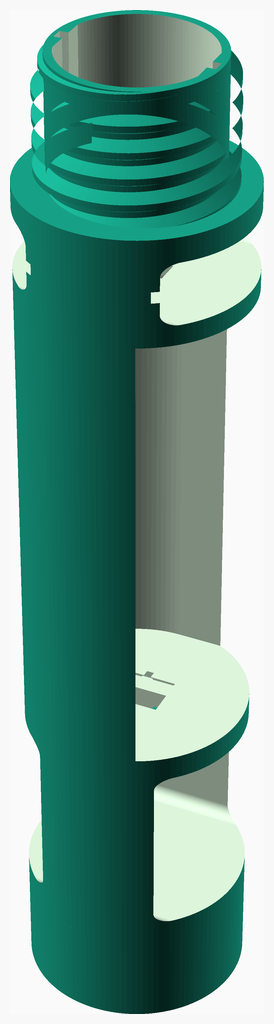
SSNvB/assemblies/SSNvB_battery_frame_assembled.png
