hotwolf/LoRaMeshNodes/SSNvB/assemblies/SSNvB_core_assembly.png

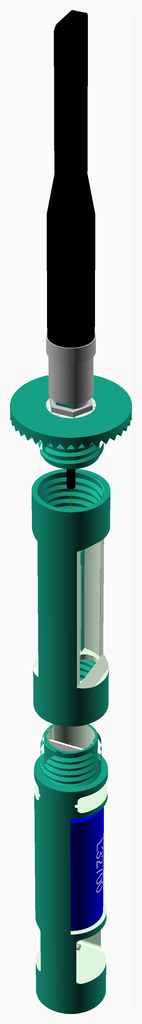
SSNvB/assemblies/SSNvB_core_assembly.png
