hotwolf/LoRaMeshNodes/SSNvB/assemblies/SSNvB_pipe_assembled.png

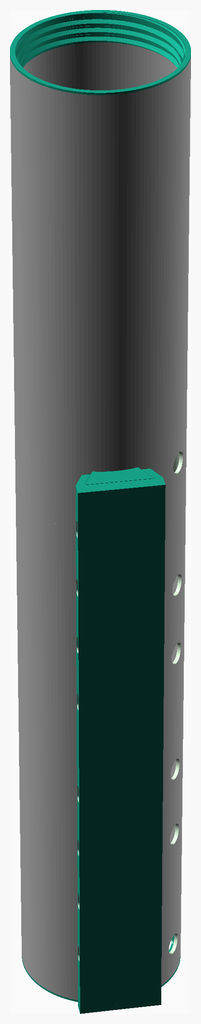
SSNvB/assemblies/SSNvB_pipe_assembled.png
