hotwolf/LoRaMeshNodes/SSNvB/assemblies/SSNvB_pipe_assembly.png

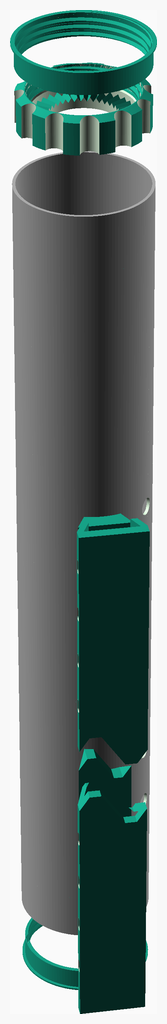
SSNvB/assemblies/SSNvB_pipe_assembly.png
