hotwolf/LoRaMeshNodes/SSNvB/assemblies/SSNvB_radio_assembled.png

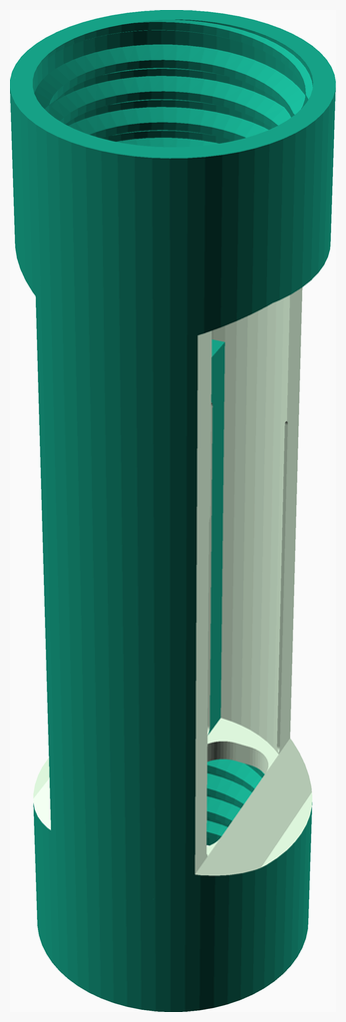
SSNvB/assemblies/SSNvB_radio_assembled.png
