hotwolf/LoRaMeshNodes/SSNvB/assemblies/SSNvB_radio_assembly.png

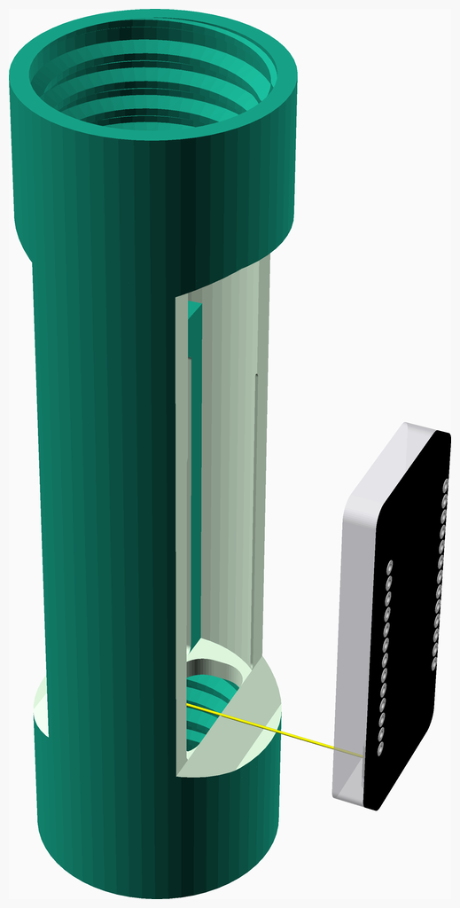
SSNvB/assemblies/SSNvB_radio_assembly.png
