hotwolf/LoRaMeshNodes/SSNvB/assemblies/SSNvB_radio_frame_assembly.png

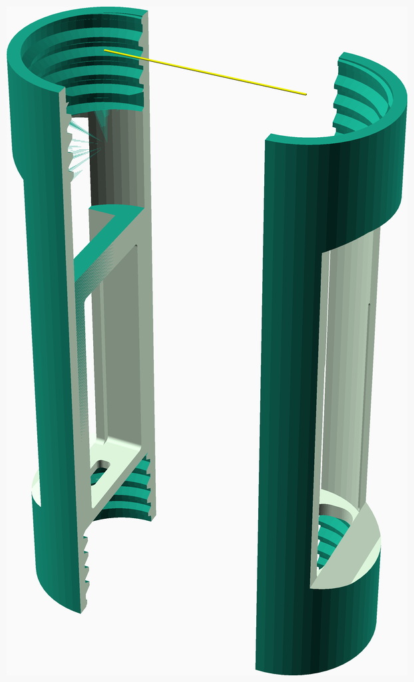
SSNvB/assemblies/SSNvB_radio_frame_assembly.png
