hotwolf/LoRaMeshNodes/SSNvB/assemblies/SSNvB_solar_assembly.png

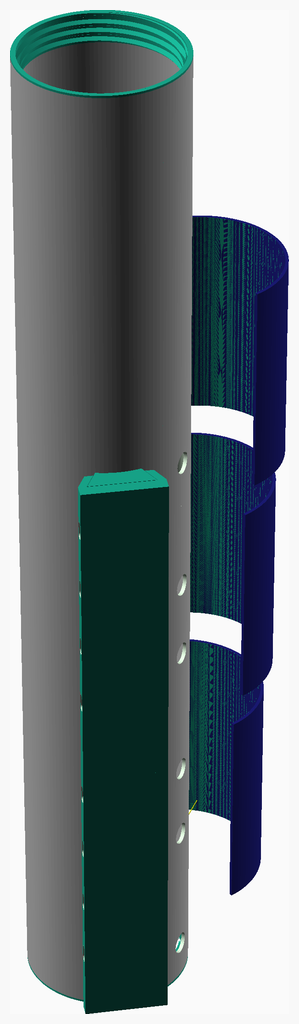
SSNvB/assemblies/SSNvB_solar_assembly.png
