hotwolf/LoRaMeshNodes/SSNvD/assemblies/SSNvD_antenna_assembled.png

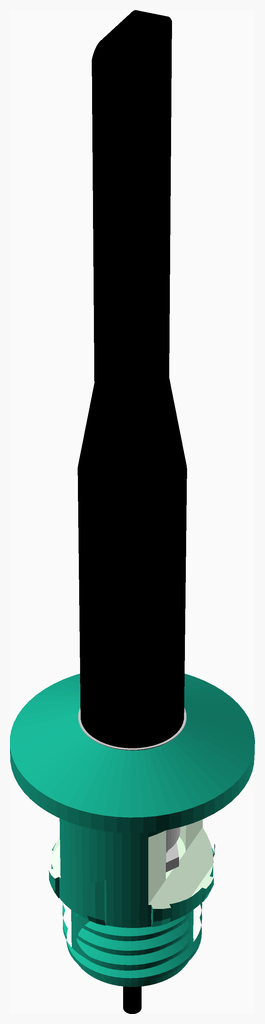
SSNvD/assemblies/SSNvD_antenna_assembled.png
