hotwolf/LoRaMeshNodes/SSNvD/assemblies/SSNvD_antenna_assembly.png

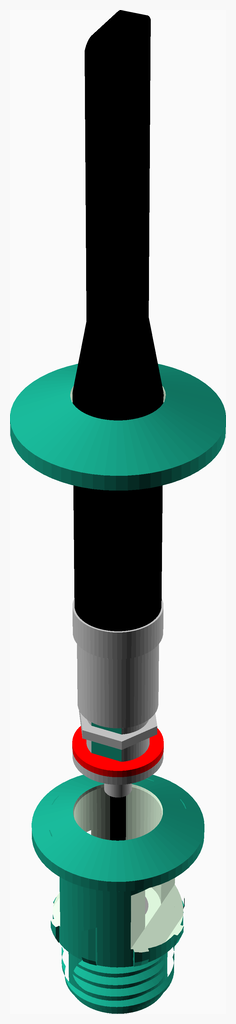
SSNvD/assemblies/SSNvD_antenna_assembly.png
