hotwolf/LoRaMeshNodes/SSNvD/assemblies/SSNvD_antenna_frame_assembled.png

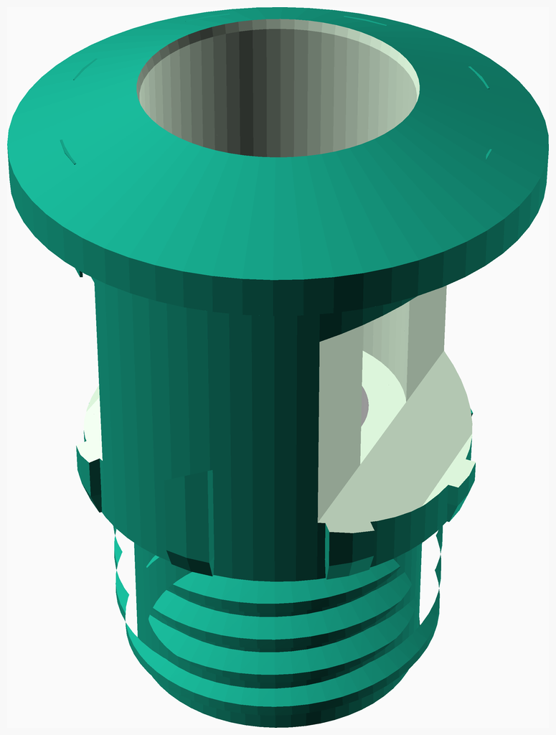
SSNvD/assemblies/SSNvD_antenna_frame_assembled.png
