hotwolf/LoRaMeshNodes/SSNvD/assemblies/SSNvD_antenna_frame_assembly.png

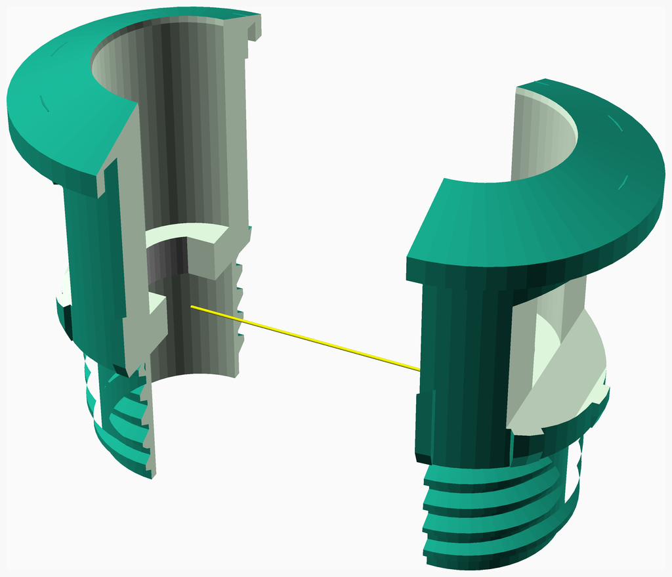
SSNvD/assemblies/SSNvD_antenna_frame_assembly.png
