hotwolf/LoRaMeshNodes/SSNvD/assemblies/SSNvD_assembly.png

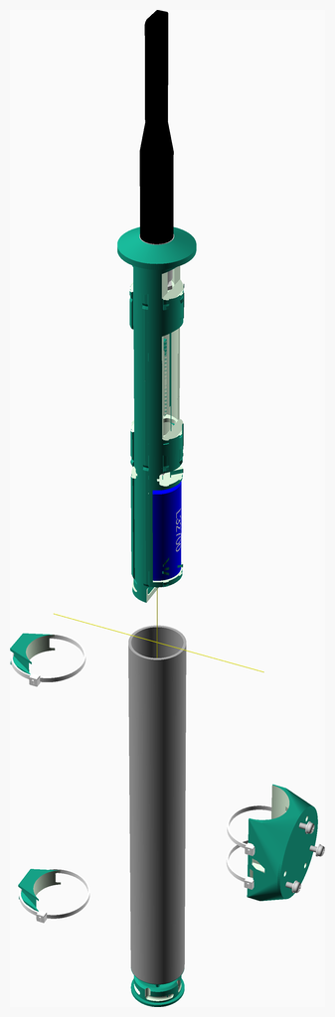
SSNvD/assemblies/SSNvD_assembly.png
