hotwolf/LoRaMeshNodes/SSNvD/assemblies/SSNvD_battery_assembled.png

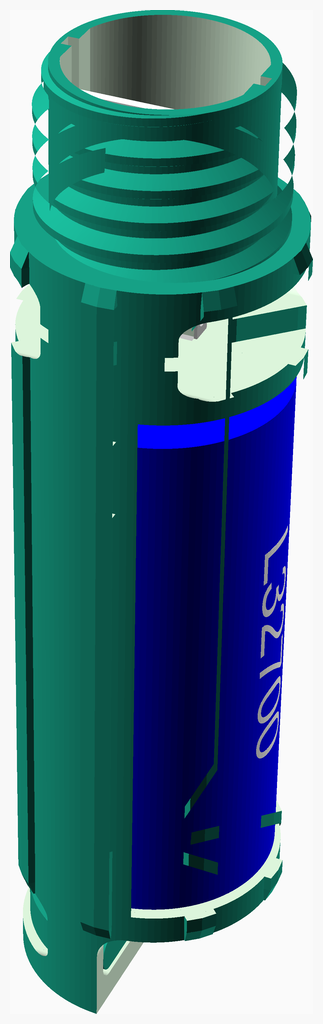
SSNvD/assemblies/SSNvD_battery_assembled.png
