hotwolf/LoRaMeshNodes/SSNvD/assemblies/SSNvD_battery_assembly.png

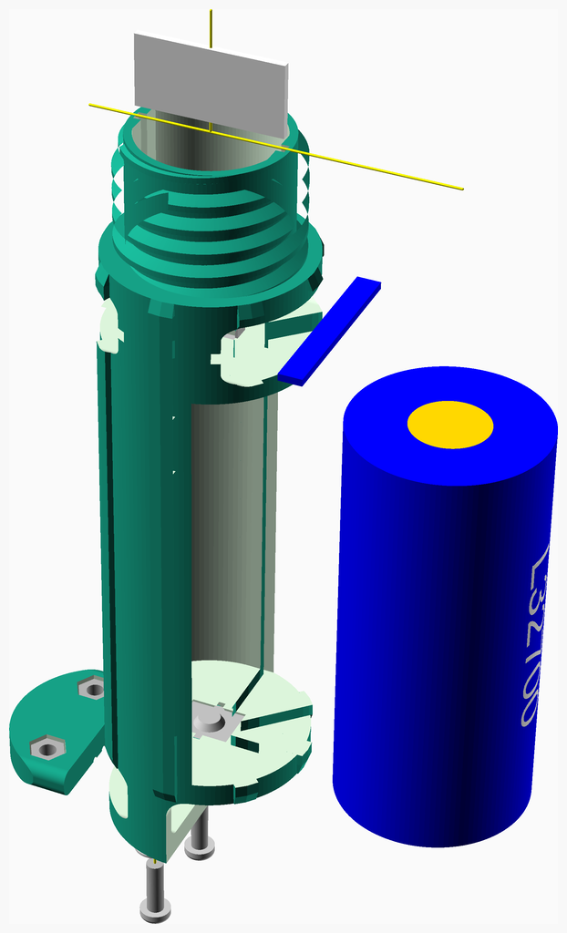
SSNvD/assemblies/SSNvD_battery_assembly.png
