hotwolf/LoRaMeshNodes/SSNvD/assemblies/SSNvD_battery_cable_clamp_assembled.png

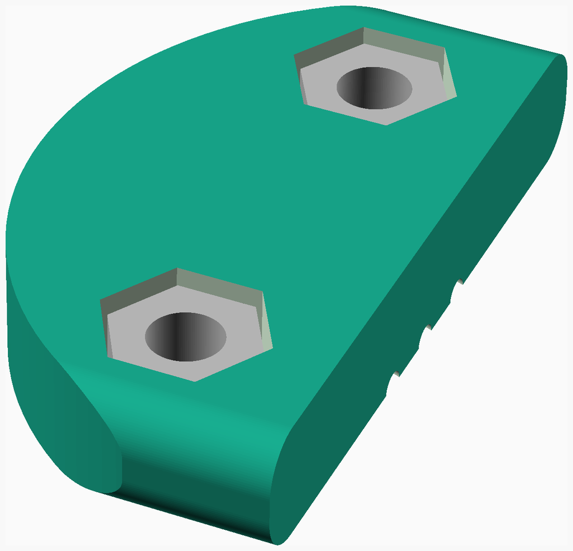
SSNvD/assemblies/SSNvD_battery_cable_clamp_assembled.png
