hotwolf/LoRaMeshNodes/SSNvD/assemblies/SSNvD_battery_cable_clamp_assembly.png

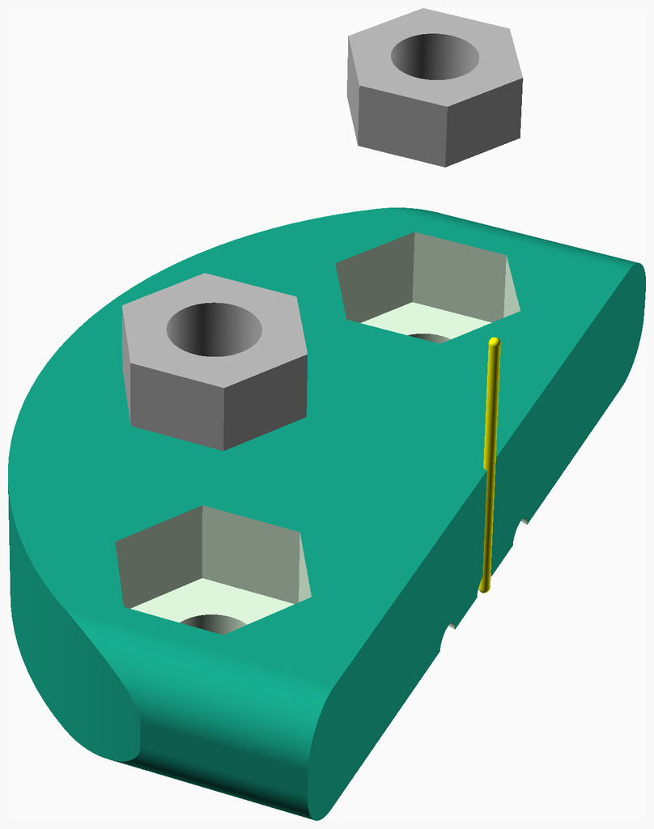
SSNvD/assemblies/SSNvD_battery_cable_clamp_assembly.png
