hotwolf/LoRaMeshNodes/SSNvD/assemblies/SSNvD_battery_frame_assembled.png

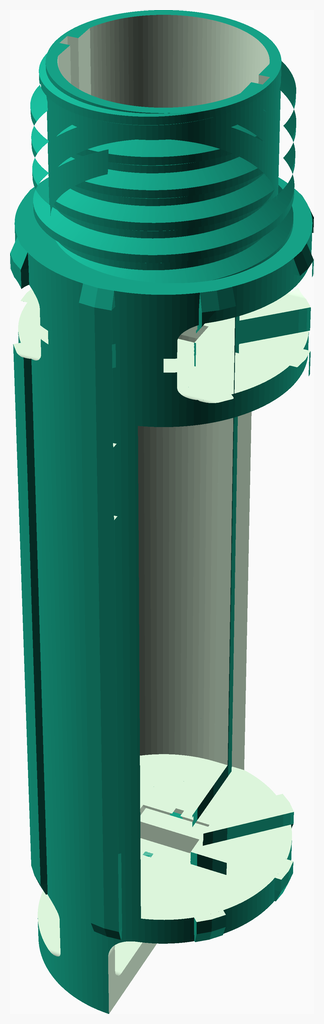
SSNvD/assemblies/SSNvD_battery_frame_assembled.png
