hotwolf/LoRaMeshNodes/SSNvD/assemblies/SSNvD_solar_mount_assembled.png

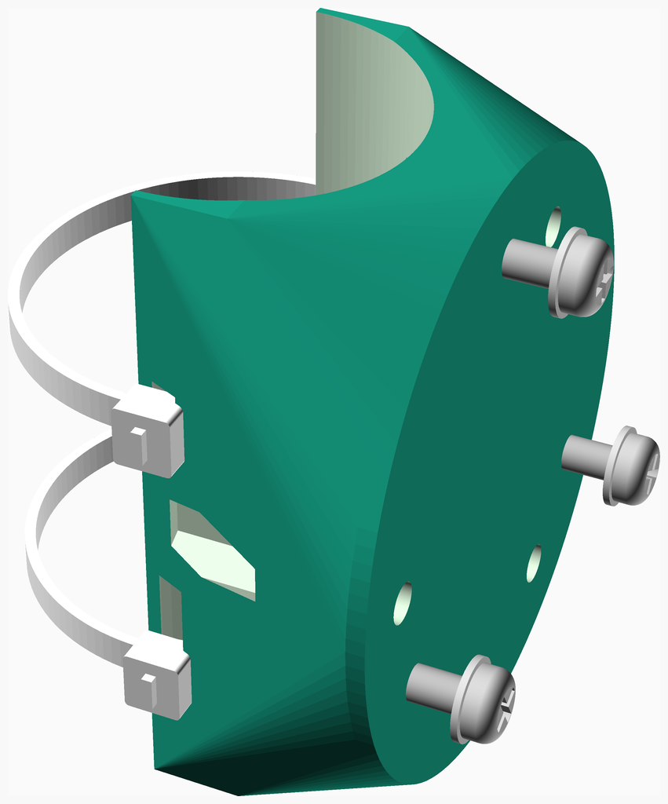
SSNvD/assemblies/SSNvD_solar_mount_assembled.png
