hotwolf/LoRaMeshNodes/SSNvD/assemblies/SSNvD_solar_mount_assembly.png

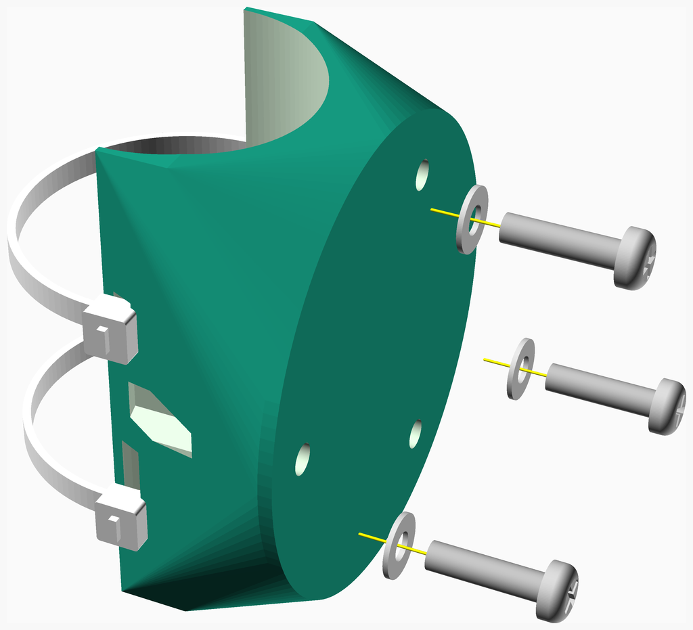
SSNvD/assemblies/SSNvD_solar_mount_assembly.png
