hotwolf/LoRaMeshNodes/SSNvD/assemblies/SSNvD_spacer_assembled.png

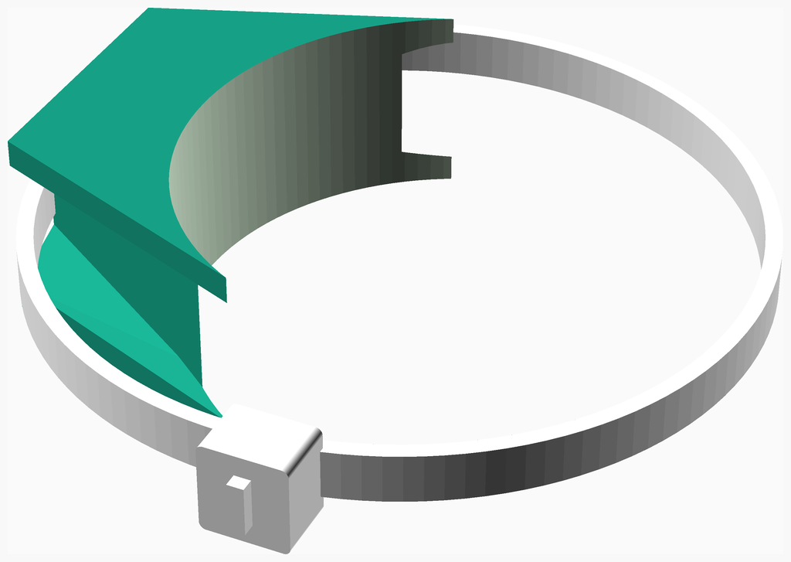
SSNvD/assemblies/SSNvD_spacer_assembled.png
