hotwolf/LoRaMeshNodes/SSNvD/assemblies/SSNvD_top_assembly.png

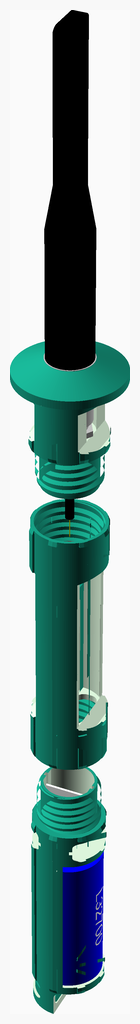
SSNvD/assemblies/SSNvD_top_assembly.png
